ardymarky/TORCH/solidworks/rubberextrusion2.SLDPRT

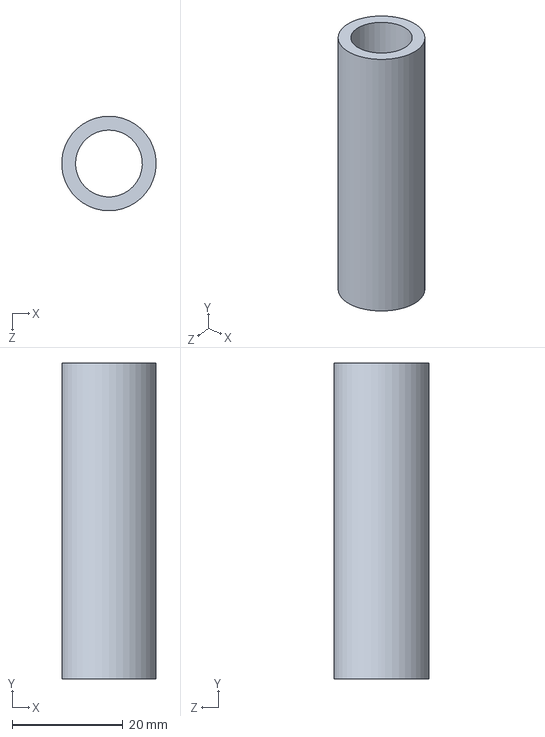
[picture p7: CAD file, 2025-04-05]
solidworks/rubberextrusion2.SLDPRT
17.0 x 57.0 x 17.0 mm
