ardymarky/TORCH/solidworks/tpu_extrusion2.SLDPRT

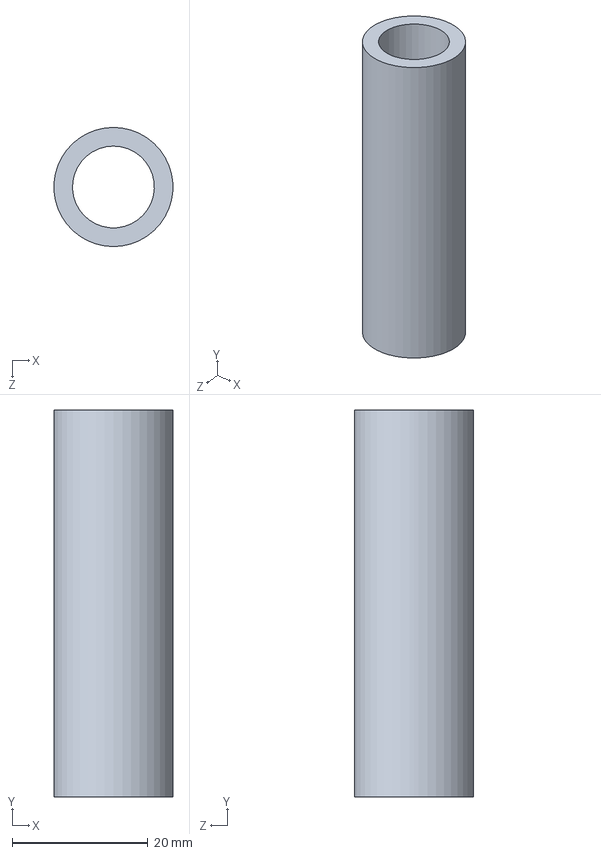
[picture p8: CAD file, 2025-04-05]
solidworks/tpu_extrusion2.SLDPRT
17.5 x 57.0 x 17.6 mm
