ardymarky/TORCH/solidworks/tpu_extrusion.SLDPRT

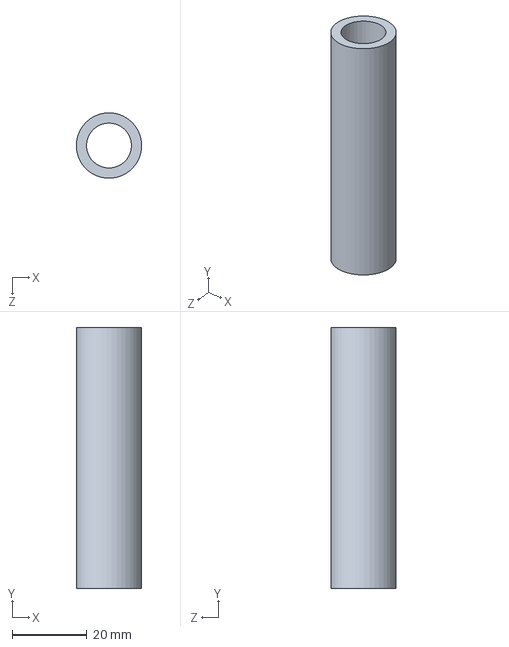
[picture p9: CAD file, 2025-04-05]
solidworks/tpu_extrusion.SLDPRT
17.5 x 70.0 x 17.5 mm
