ardymarky/TORCH/solidworks/endstop_2point0_1.SLDPRT

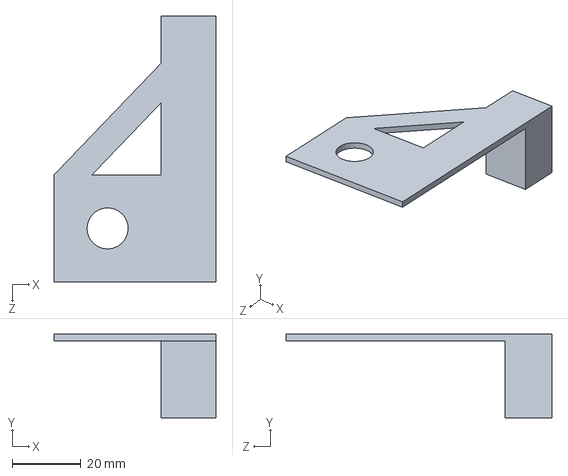
[picture p10: CAD file, 2025-04-04]
solidworks/endstop_2point0_1.SLDPRT
47.3 x 24.5 x 77.6 mm
