ardymarky/TORCH/solidworks/endstop_lidar.SLDPRT

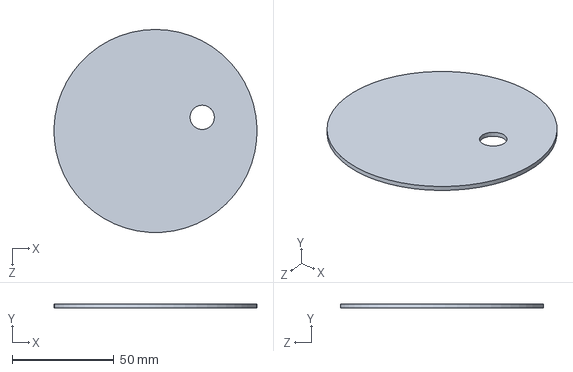
[picture p11: CAD file, 2025-04-04]
solidworks/endstop_lidar.SLDPRT
100.0 x 2.00 x 100.0 mm
