ardymarky/TORCH/solidworks/AC_DC_TOP_PLATE.SLDPRT

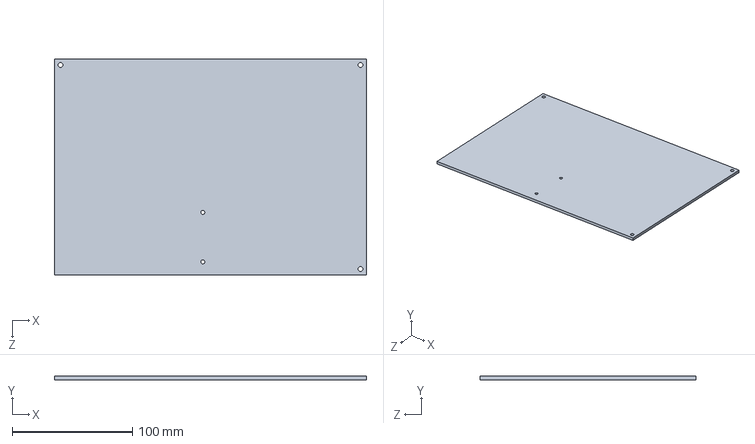
[picture p12: CAD file, 2025-04-02]
solidworks/AC_DC_TOP_PLATE.SLDPRT
260.0 x 3.00 x 180.0 mm
