ardymarky/TORCH/solidworks/xrailmount.SLDPRT

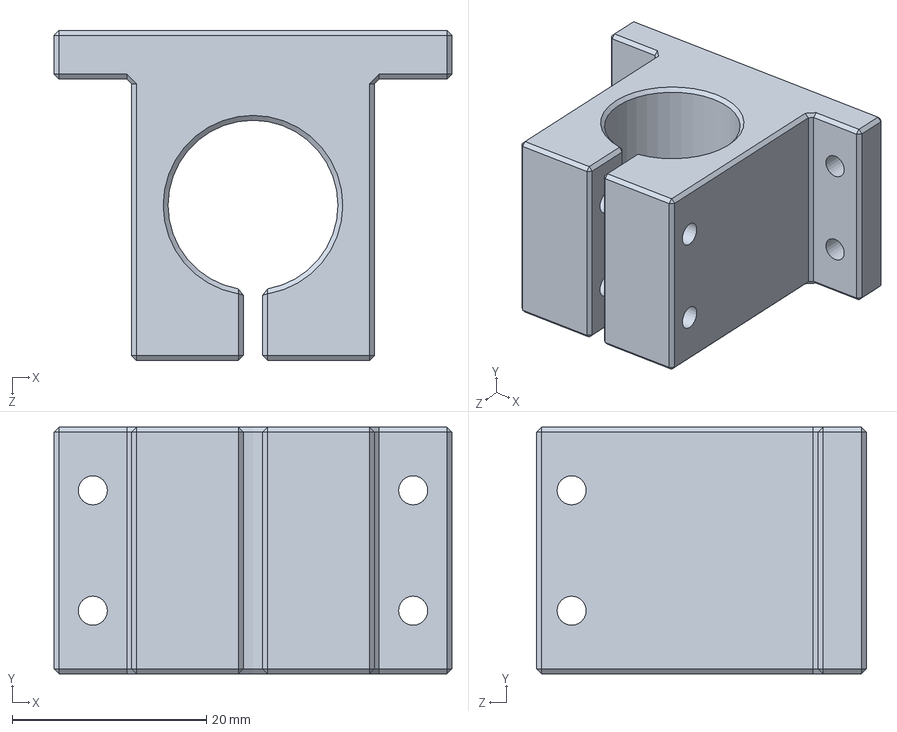
[picture p13: CAD file, 2025-03-26]
solidworks/xrailmount.SLDPRT
41.0 x 25.4 x 34.0 mm
