ardymarky/TORCH/solidworks/dronewiring.SLDPRT

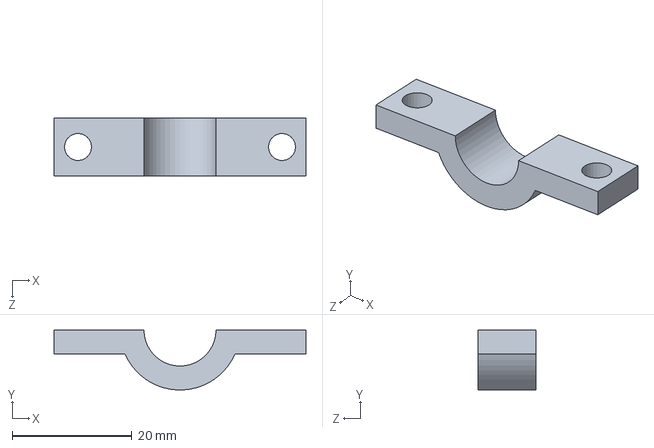
[picture p14: CAD file, 2025-03-26]
solidworks/dronewiring.SLDPRT
42.0 x 9.98 x 9.75 mm
