ardymarky/TORCH/solidworks/Linear_rail_hold_V4_2_new.SLDPRT

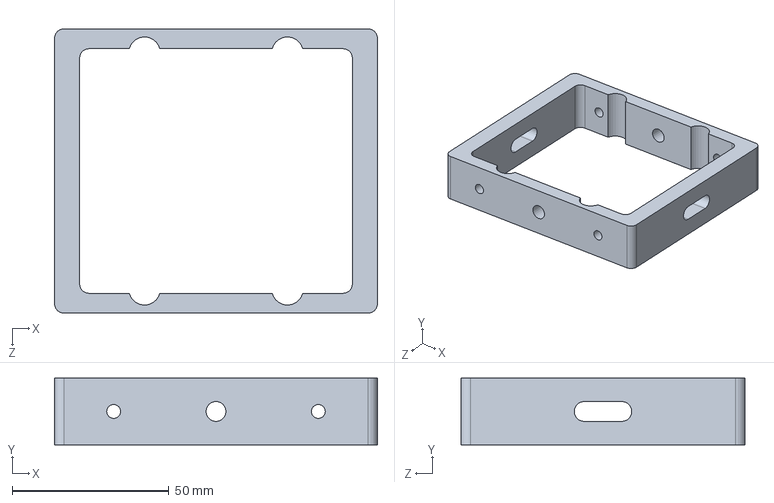
[picture p15: CAD file, 2025-03-25]
solidworks/Linear_rail_hold_V4_2_new.SLDPRT
103.0 x 21.3 x 90.7 mm
