ardymarky/TORCH/solidworks/dronewirehinge.SLDPRT

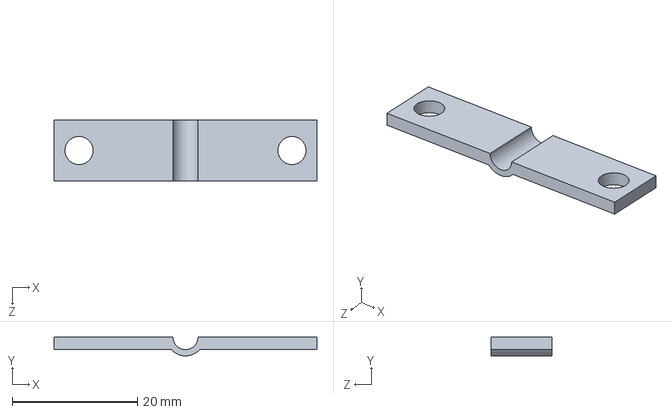
[picture p16: CAD file, 2025-03-25]
solidworks/dronewirehinge.SLDPRT
42.0 x 2.99 x 9.75 mm
