ardymarky/TORCH/solidworks/Rod_mount_two holes.SLDPRT

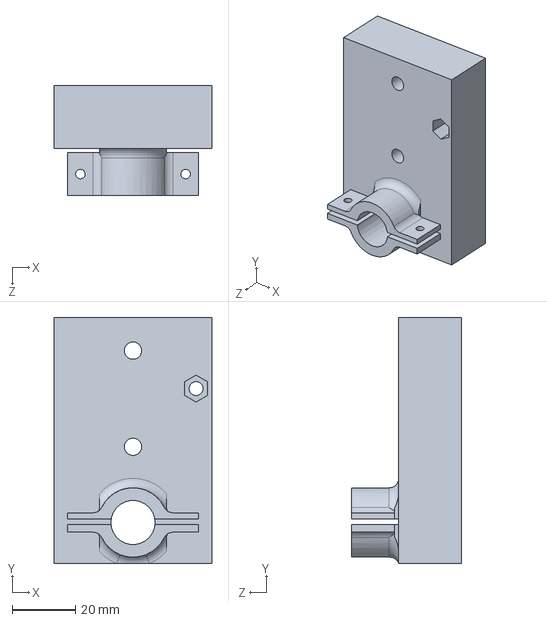
[picture p17: CAD file, 2025-03-25]
solidworks/Rod_mount_two holes.SLDPRT
50.0 x 78.0 x 35.0 mm
