ardymarky/TORCH/solidworks/Wheel_encoder_mount_two _hole.SLDPRT

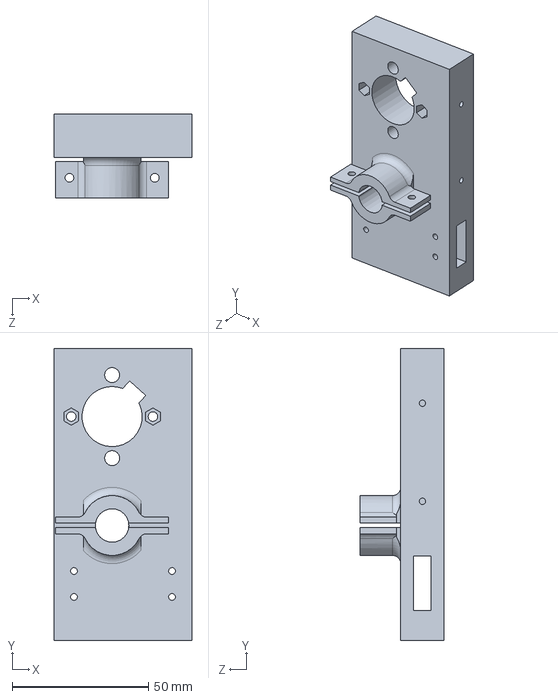
[picture p18: CAD file, 2025-03-25]
solidworks/Wheel_encoder_mount_two _hole.SLDPRT
50.6 x 107.2 x 31.0 mm
