ardymarky/TORCH/solidworks/TORCH_PULLEY_WHEEL.SLDPRT

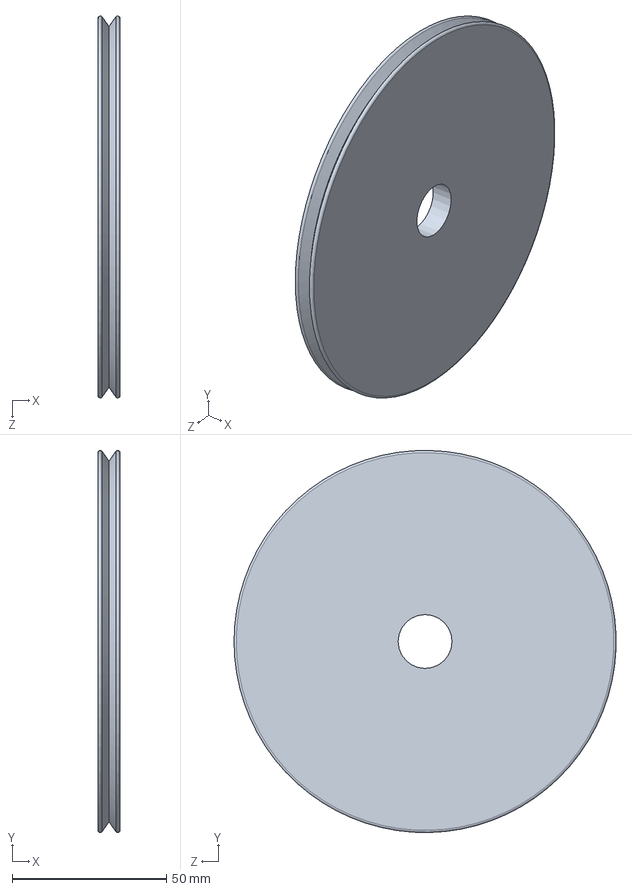
[picture p19: CAD file, 2025-03-25]
solidworks/TORCH_PULLEY_WHEEL.SLDPRT
7.14 x 123.8 x 123.8 mm
