ardymarky/TORCH/solidworks/squarerubber_1.SLDPRT

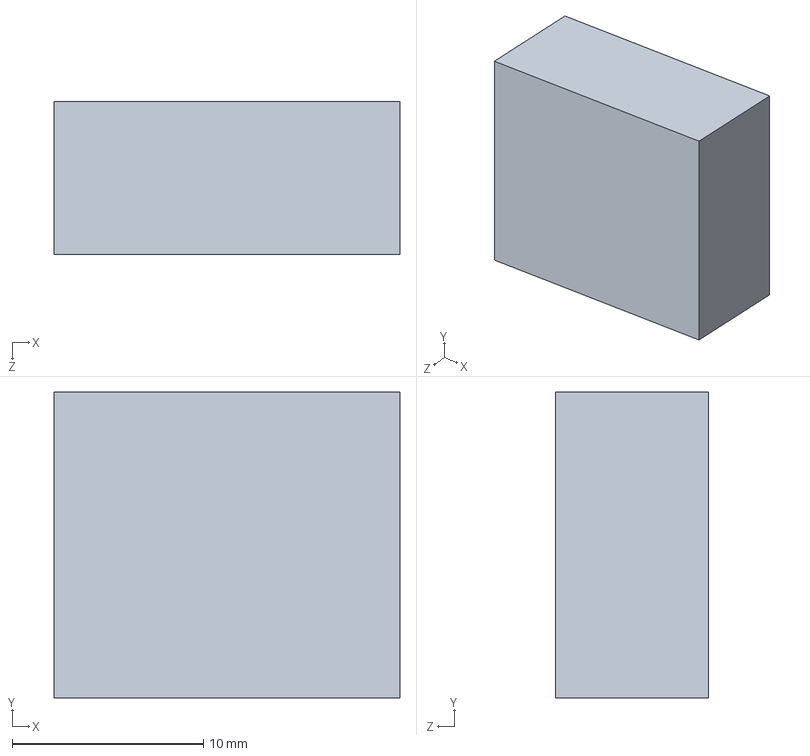
[picture p20: CAD file, 2025-03-19]
solidworks/squarerubber_1.SLDPRT
18.1 x 16.0 x 8.00 mm
