ardymarky/TORCH/solidworks/squarerubber.SLDPRT

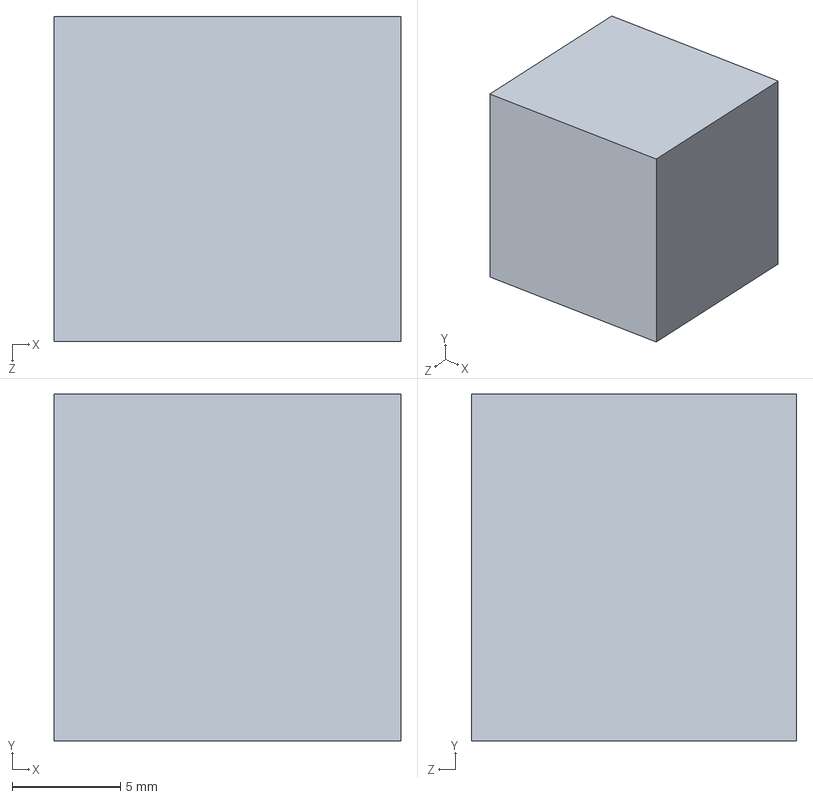
[picture p21: CAD file, 2025-03-19]
solidworks/squarerubber.SLDPRT
16.0 x 16.0 x 15.0 mm
