ardymarky/TORCH/solidworks/Wheel_encoder_mount_carbon_rod_V2.STL

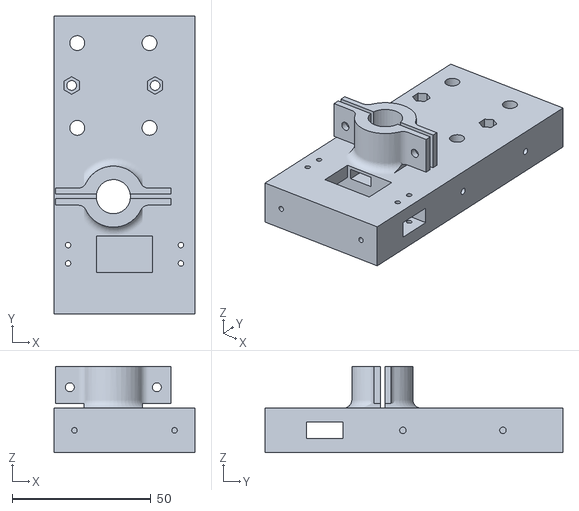
[picture p22: CAD file, 2025-03-18]
solidworks/Wheel_encoder_mount_carbon_rod_V2.STL
50.6 x 107.2 x 31.0
