ardymarky/TORCH/solidworks/Rod_mount_carbon_rod_V2.SLDPRT

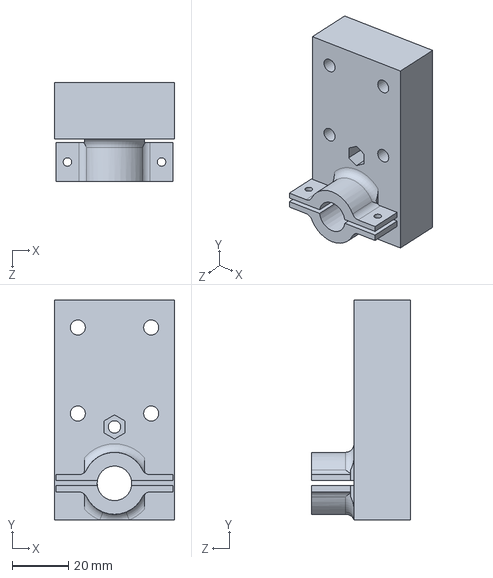
[picture p23: CAD file, 2025-03-18]
solidworks/Rod_mount_carbon_rod_V2.SLDPRT
42.6 x 78.0 x 35.0 mm
