ardymarky/TORCH/solidworks/guard_bottom1_combo.SLDPRT

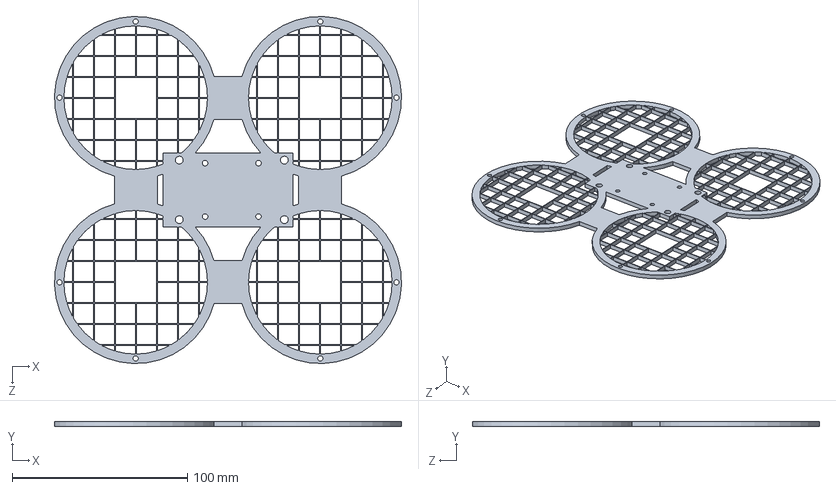
[picture p24: CAD file, 2025-03-18]
solidworks/guard_bottom1_combo.SLDPRT
198.2 x 3.00 x 198.2 mm
