ardymarky/TORCH/solidworks/tpu_piece_rod_2.SLDPRT

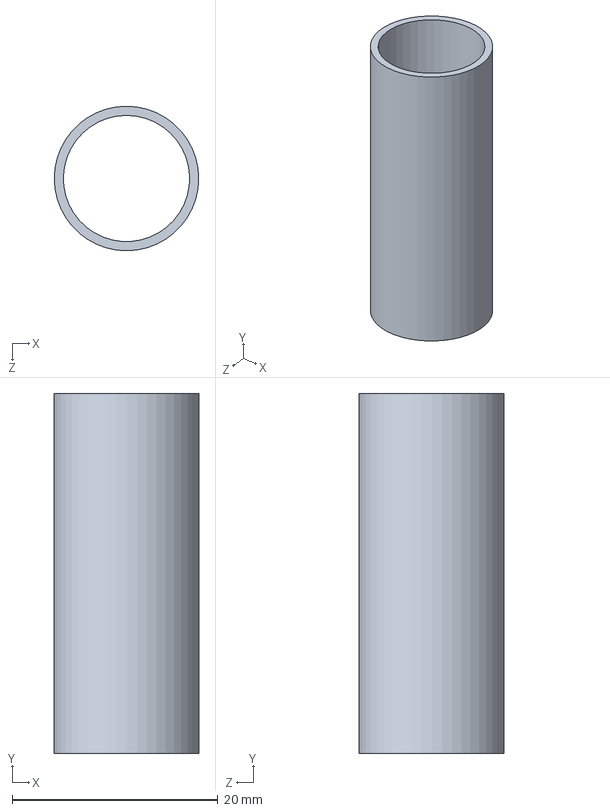
[picture p25: CAD file, 2025-03-07]
solidworks/tpu_piece_rod_2.SLDPRT
14.1 x 35.0 x 14.1 mm
