ardymarky/TORCH/solidworks/Rod_mount.SLDPRT

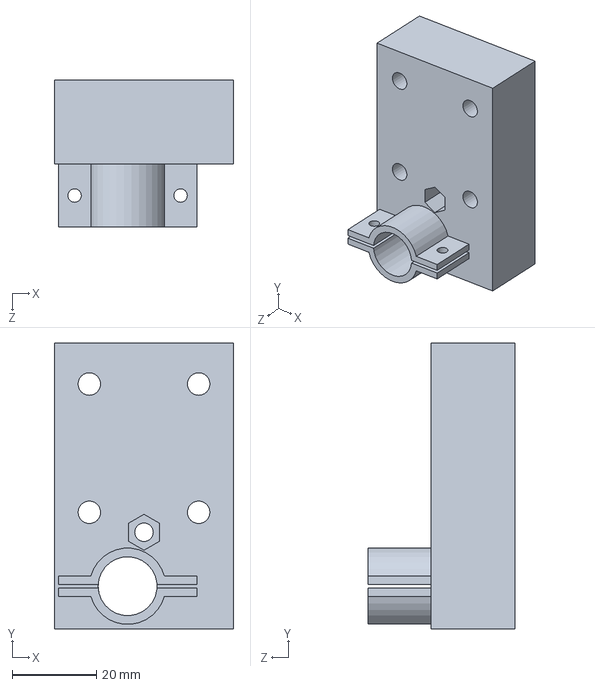
[picture p26: CAD file, 2025-03-07]
solidworks/Rod_mount.SLDPRT
42.6 x 68.0 x 35.0 mm
