ardymarky/TORCH/solidworks/Wheel_encoder_mount_v2_alteration.SLDPRT

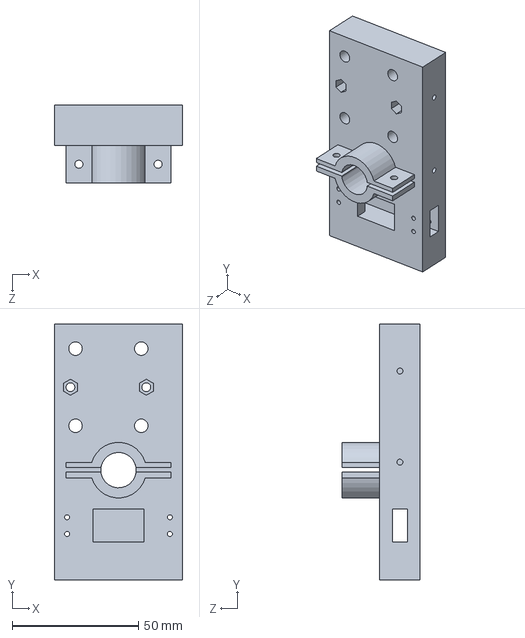
[picture p27: CAD file, 2025-03-07]
solidworks/Wheel_encoder_mount_v2_alteration.SLDPRT
50.6 x 101.2 x 31.0 mm
