ardymarky/TORCH/solidworks/tpu_piece_SMALLER.SLDPRT

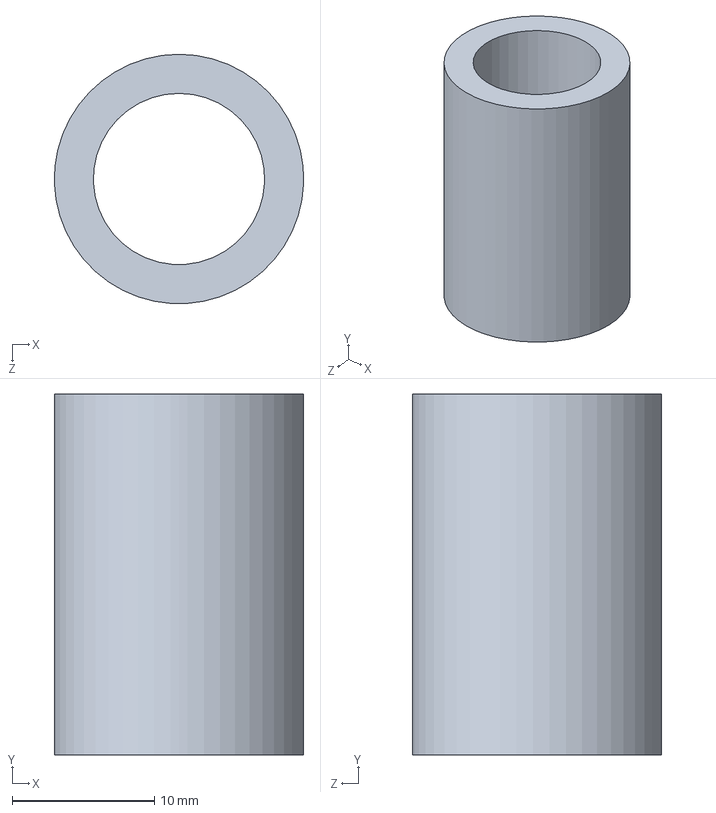
[picture p28: CAD file, 2025-03-06]
solidworks/tpu_piece_SMALLER.SLDPRT
17.5 x 25.4 x 17.6 mm
