ardymarky/TORCH/solidworks/Rod_mount_1mm_bearing_through_hole.SLDPRT

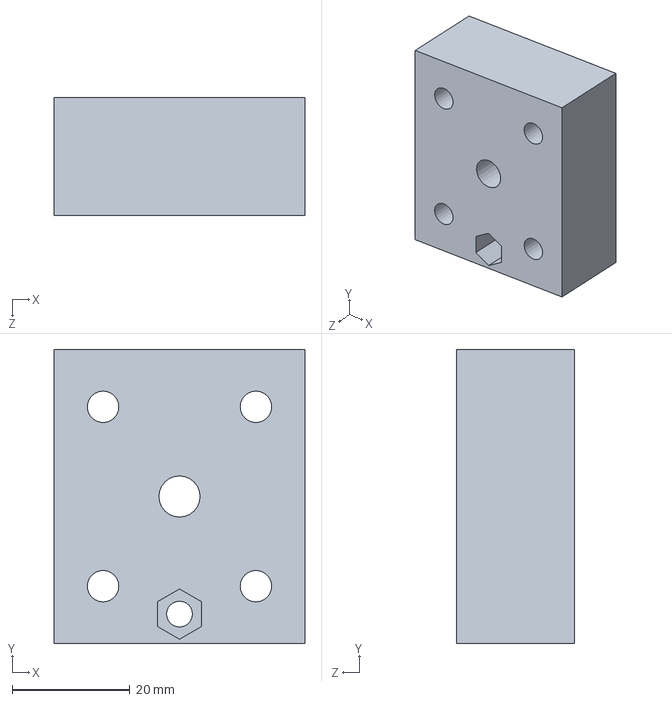
[picture p29: CAD file, 2025-03-06]
solidworks/Rod_mount_1mm_bearing_through_hole.SLDPRT
42.6 x 50.0 x 20.0 mm
