ardymarky/TORCH/solidworks/tpu_piece_rod.SLDPRT

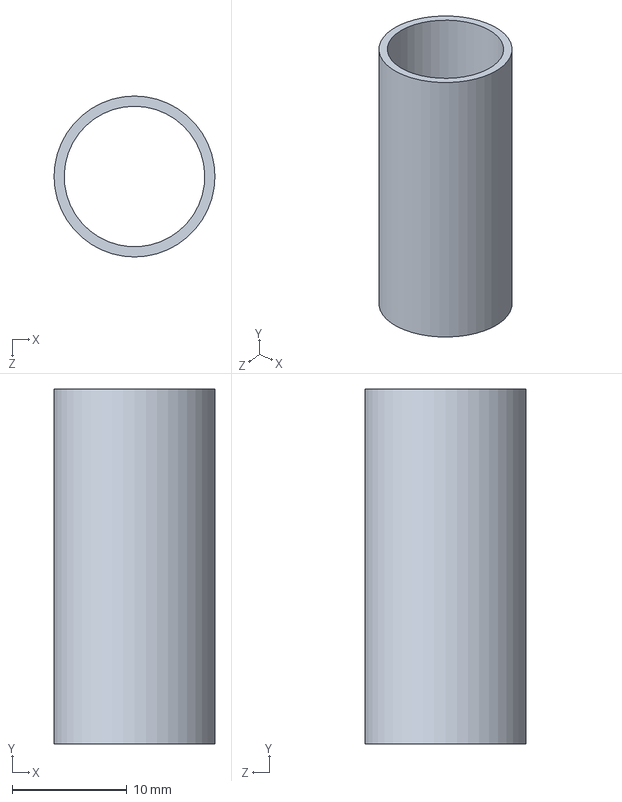
[picture p30: CAD file, 2025-03-06]
solidworks/tpu_piece_rod.SLDPRT
14.1 x 31.0 x 14.1 mm
