ardymarky/TORCH/solidworks/Wheel_encoder_mount_v2_alteration_thickness.SLDPRT

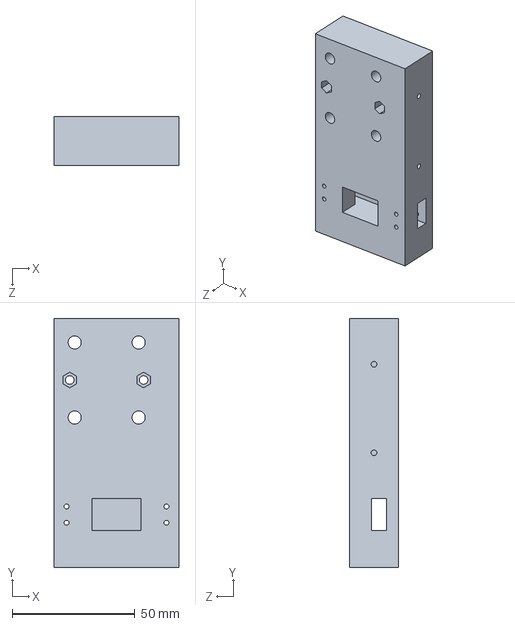
[picture p31: CAD file, 2025-02-27]
solidworks/Wheel_encoder_mount_v2_alteration_thickness.SLDPRT
50.6 x 101.2 x 20.0 mm
