ardymarky/TORCH/solidworks/clampBottomPrint.SLDPRT

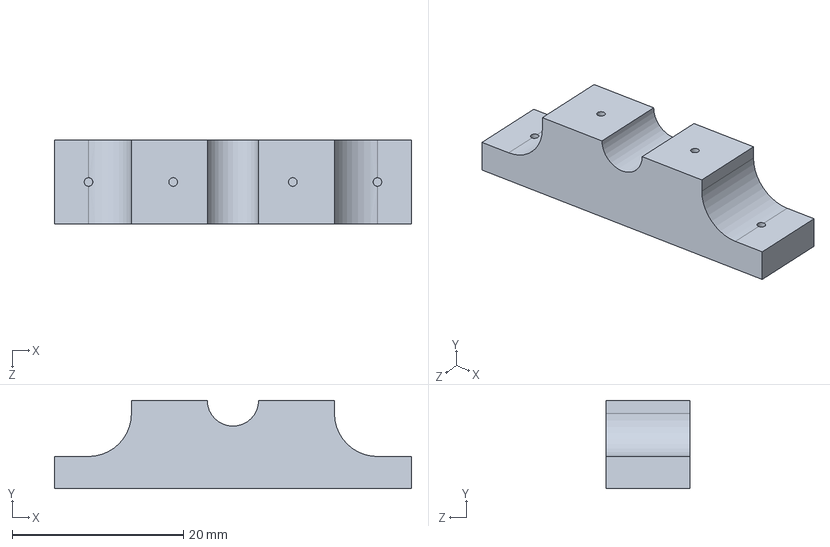
[picture p32: CAD file, 2025-02-19]
solidworks/clampBottomPrint.SLDPRT
41.7 x 10.3 x 9.87 mm
