ardymarky/TORCH/solidworks/quadBasePrintedClamps.SLDPRT

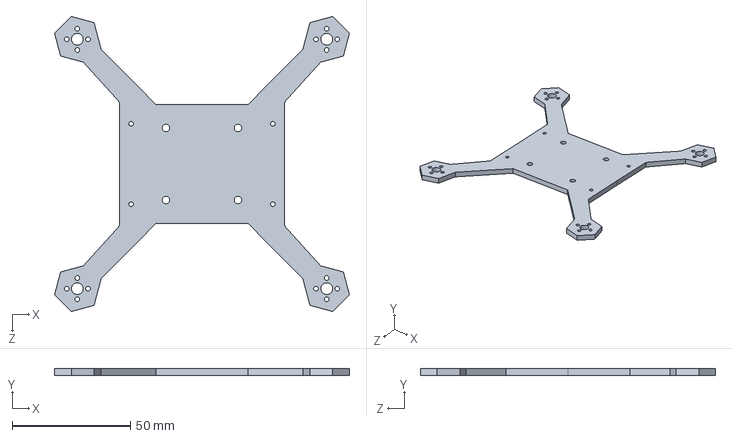
[picture p33: CAD file, 2025-02-19]
solidworks/quadBasePrintedClamps.SLDPRT
124.8 x 3.00 x 124.8 mm
