ardymarky/TORCH/solidworks/clampTopPrint.SLDPRT

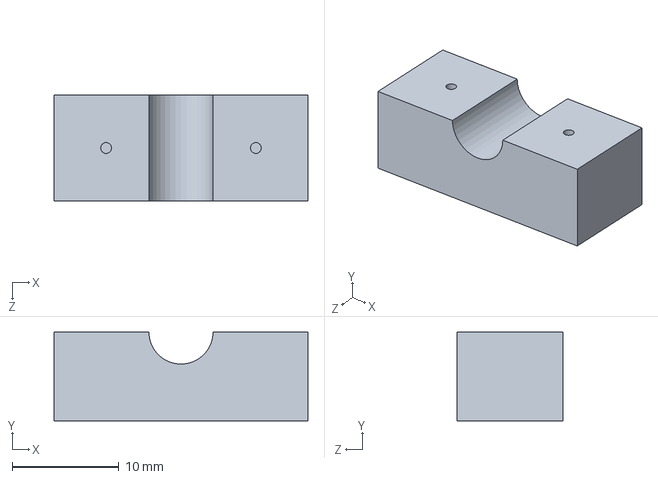
[picture p34: CAD file, 2025-02-19]
solidworks/clampTopPrint.SLDPRT
23.7 x 8.32 x 9.87 mm
