ardymarky/TORCH/solidworks/xlinearrailmount.SLDPRT

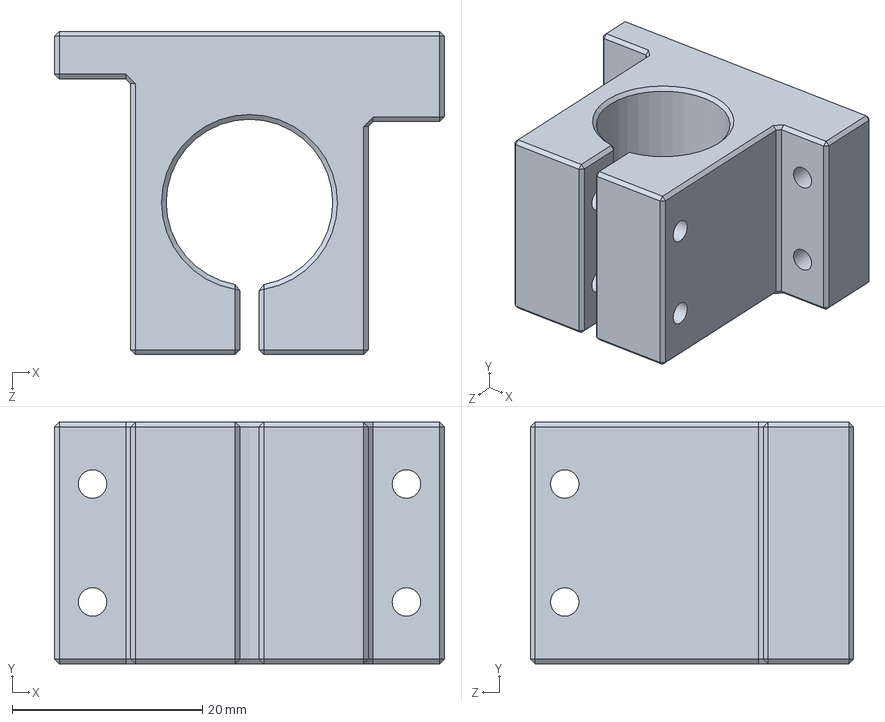
[picture p35: CAD file, 2025-02-06]
solidworks/xlinearrailmount.SLDPRT
41.0 x 25.4 x 34.0 mm
