ardymarky/TORCH/solidworks/Shaft support SK12.SLDPRT

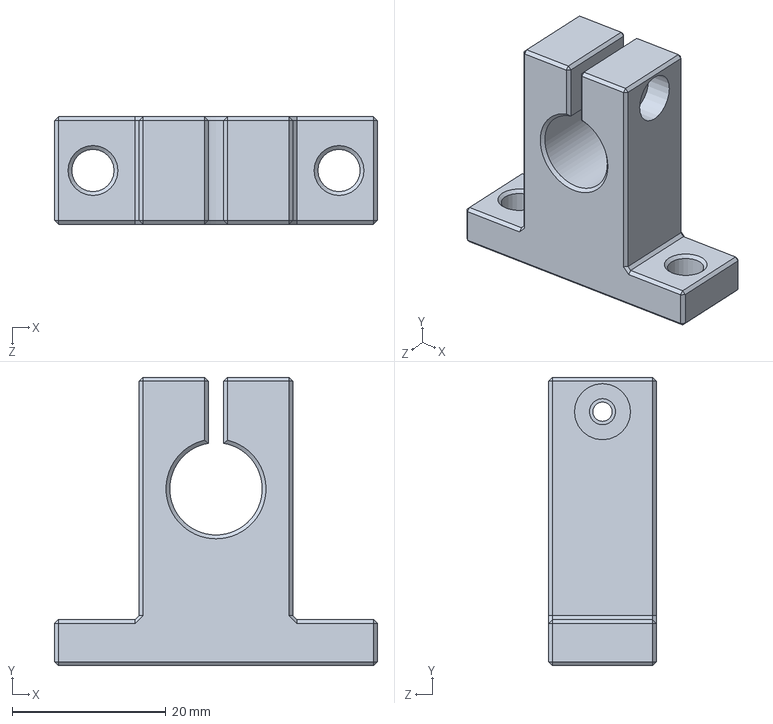
[picture p36: CAD file, 2025-02-06]
solidworks/Shaft support SK12.SLDPRT
42.0 x 37.5 x 14.0 mm
