ardymarky/TORCH/solidworks/endstop_2point0.SLDPRT

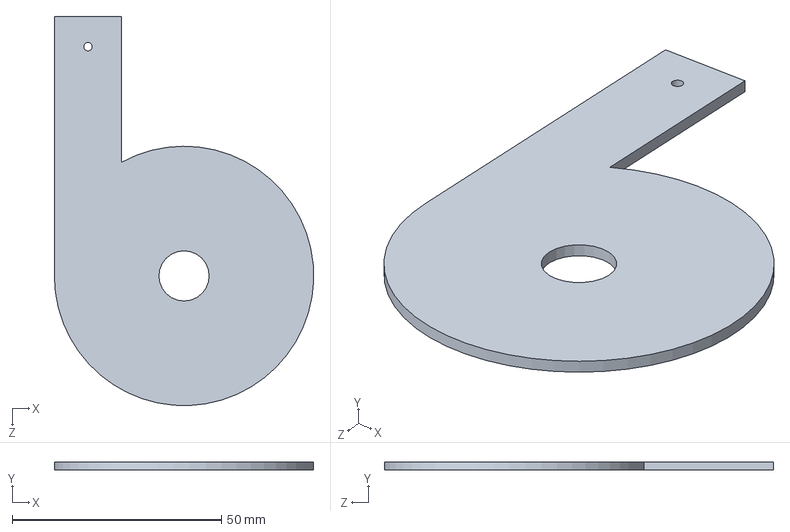
[picture p37: CAD file, 2025-01-28]
solidworks/endstop_2point0.SLDPRT
62.0 x 2.00 x 93.0 mm
