ardymarky/TORCH/solidworks/AC_DC_TOP_PLATE_STANDOFF.SLDPRT

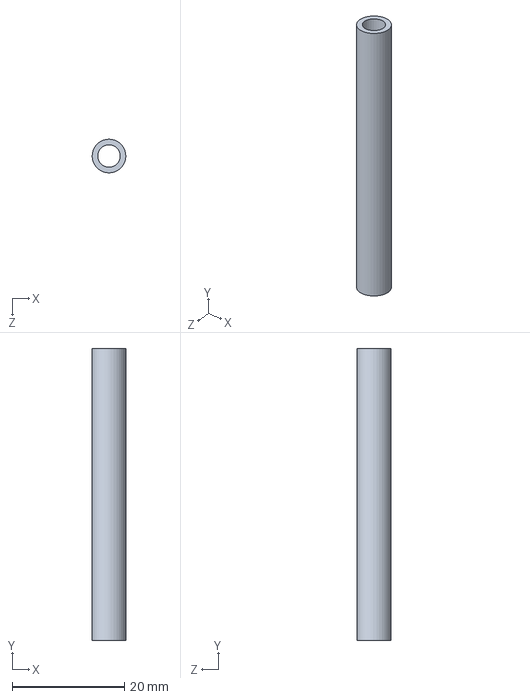
[picture p38: CAD file, 2024-12-06]
solidworks/AC_DC_TOP_PLATE_STANDOFF.SLDPRT
5.99 x 52.0 x 6.00 mm
