ardymarky/TORCH/solidworks/Relay_Standoff.SLDPRT

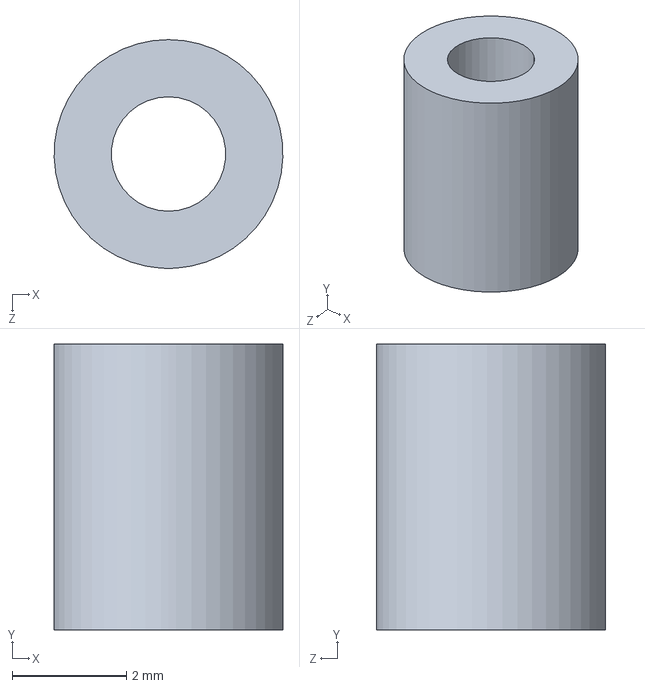
[picture p39: CAD file, 2024-12-06]
solidworks/Relay_Standoff.SLDPRT
4.00 x 5.00 x 4.00 mm
