ardymarky/TORCH/solidworks/AC_DC_Converter_Mount.SLDPRT

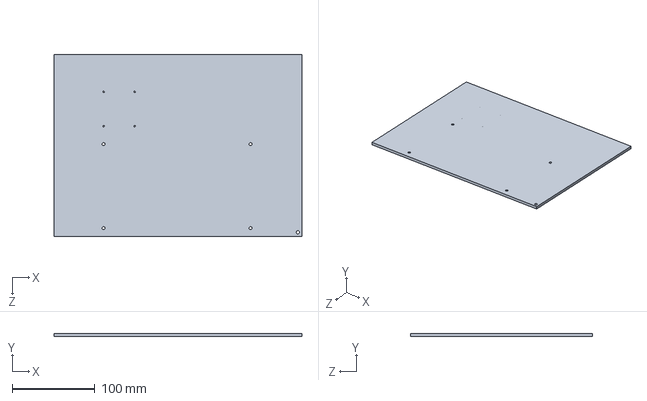
[picture p40: CAD file, 2024-12-06]
solidworks/AC_DC_Converter_Mount.SLDPRT
300.0 x 4.00 x 220.0 mm
