ardymarky/TORCH/solidworks/Relay_cover.SLDPRT

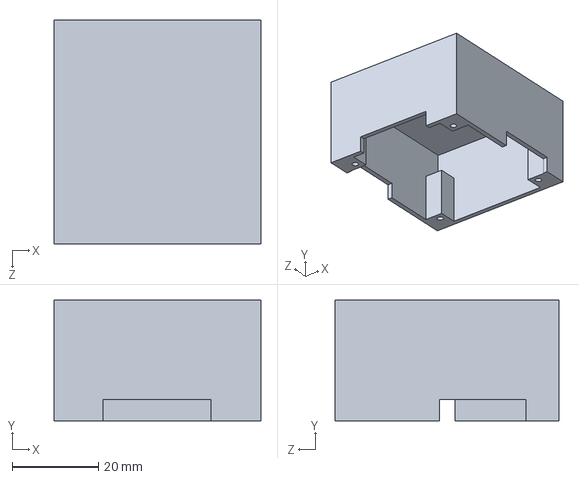
[picture p41: CAD file, 2024-12-06]
solidworks/Relay_cover.SLDPRT
48.0 x 28.0 x 52.0 mm
