ardymarky/TORCH/solidworks/PDB_Relay.SLDPRT

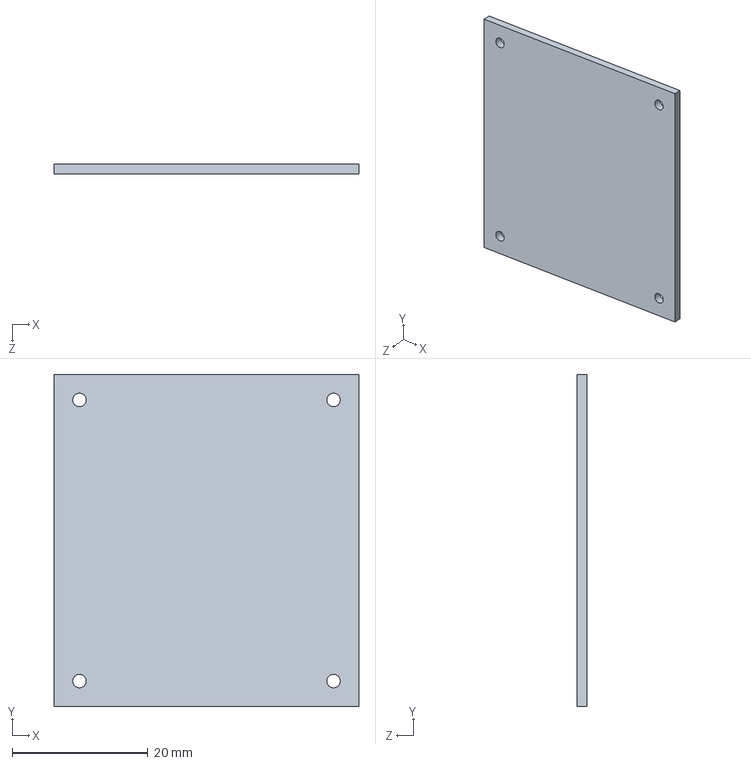
[picture p42: CAD file, 2024-12-06]
solidworks/PDB_Relay.SLDPRT
45.0 x 49.0 x 1.50 mm
