ardymarky/TORCH/solidworks/assem2.STEP

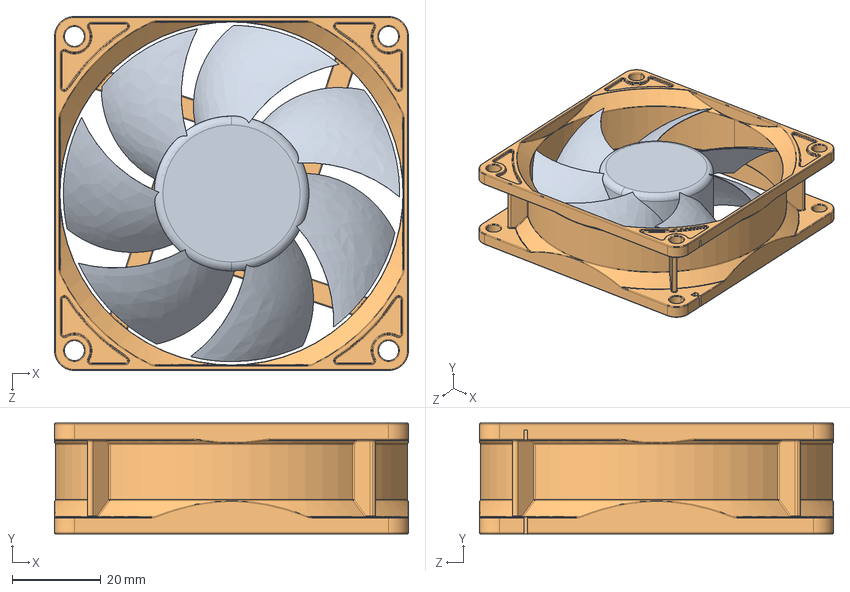
[picture p43: CAD file, 2024-12-04]
solidworks/assem2.STEP
80.0 x 25.0 x 80.0 mm
fan blades
Housing
