ardymarky/TORCH/solidworks/Power_Box.SLDPRT

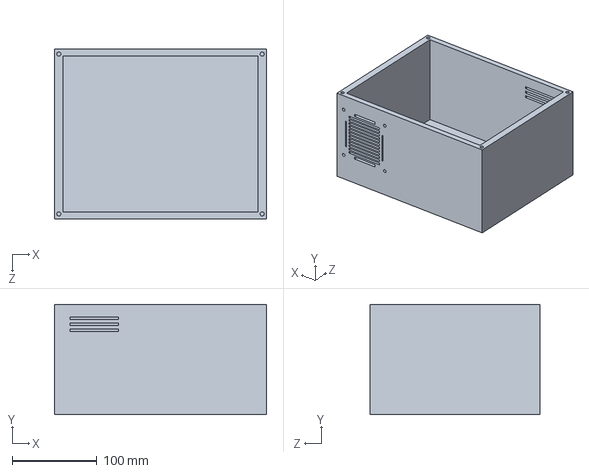
[picture p44: CAD file, 2024-12-04]
solidworks/Power_Box.SLDPRT
250.0 x 130.0 x 200.0 mm
