ardymarky/TORCH/solidworks/Pulley Wheel Standoff.STL

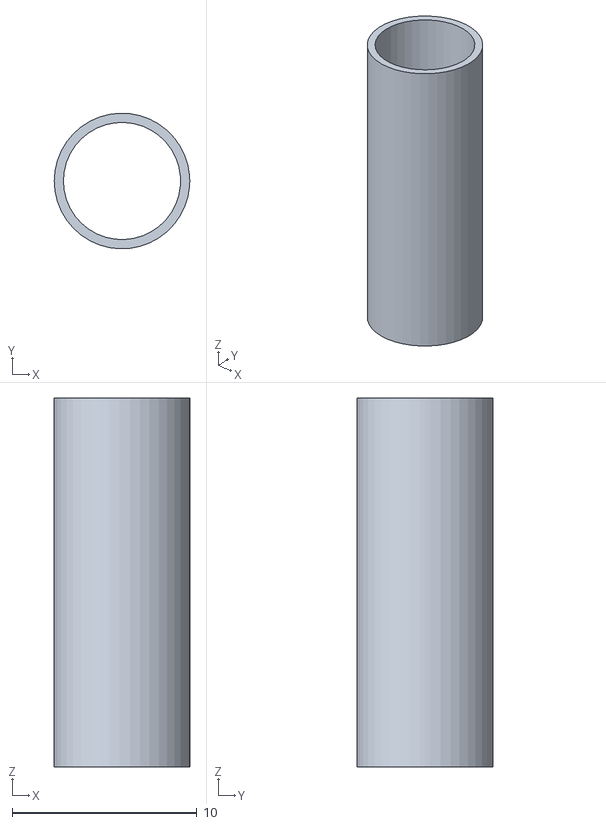
[picture p45: CAD file, 2024-12-04]
solidworks/Pulley Wheel Standoff.STL
7.35 x 7.34 x 20.0
