ardymarky/TORCH/solidworks/power connector.SLDPRT

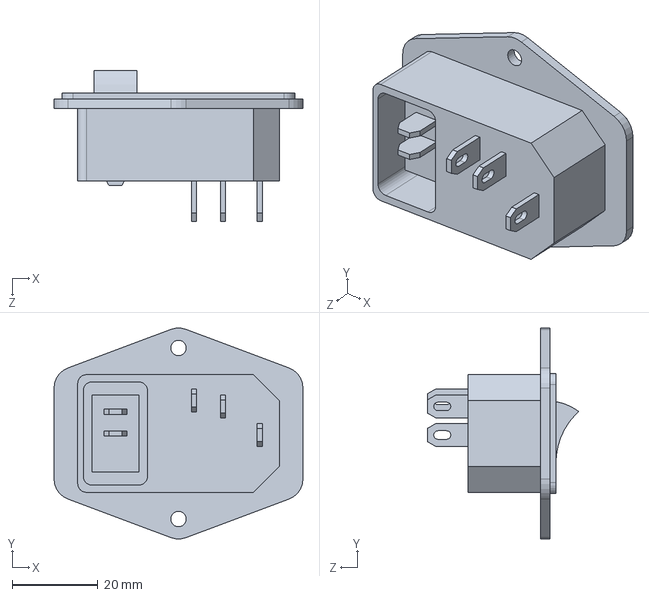
[picture p46: CAD file, 2024-12-04]
solidworks/power connector.SLDPRT
58.2 x 49.3 x 35.4 mm
