ardymarky/TORCH/solidworks/rubber_part2.SLDPRT

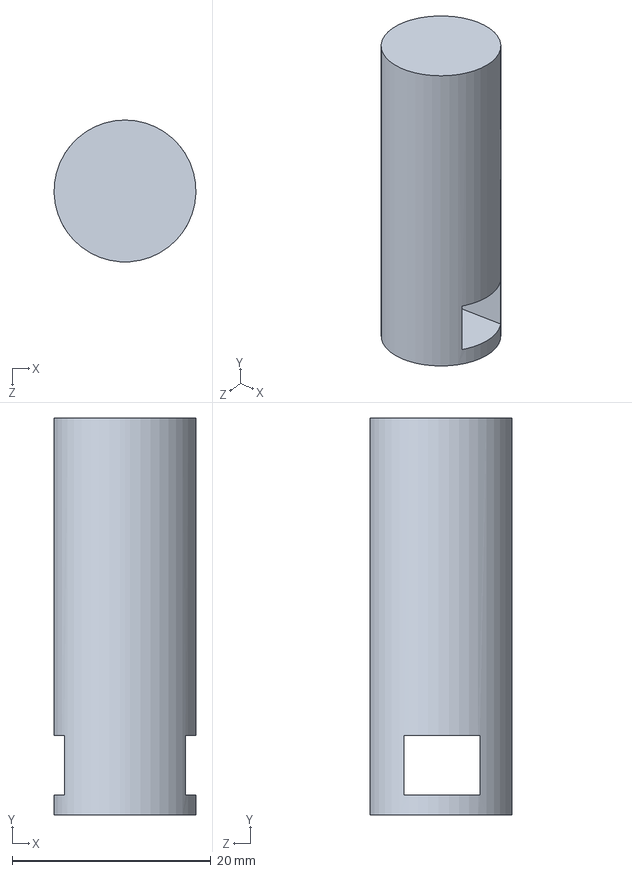
[picture p47: CAD file, 2024-12-04]
solidworks/rubber_part2.SLDPRT
14.3 x 40.0 x 14.3 mm
