ardymarky/TORCH/solidworks/rubber_p.SLDPRT

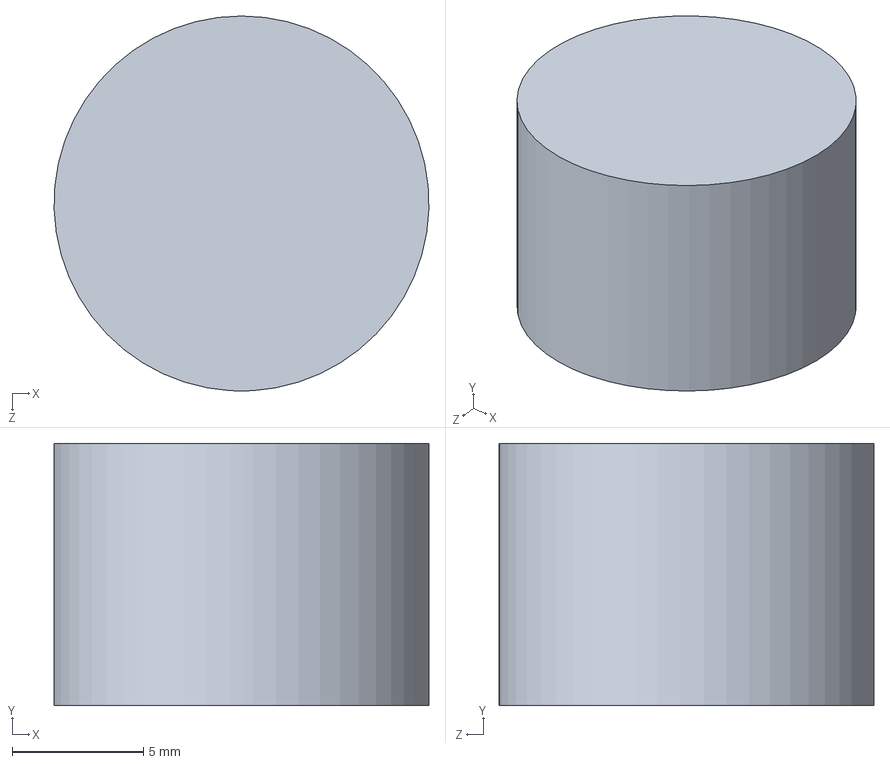
[picture p48: CAD file, 2024-11-19]
solidworks/rubber_p.SLDPRT
14.3 x 10.0 x 14.3 mm
