ardymarky/TORCH/solidworks/guard_combo.SLDPRT

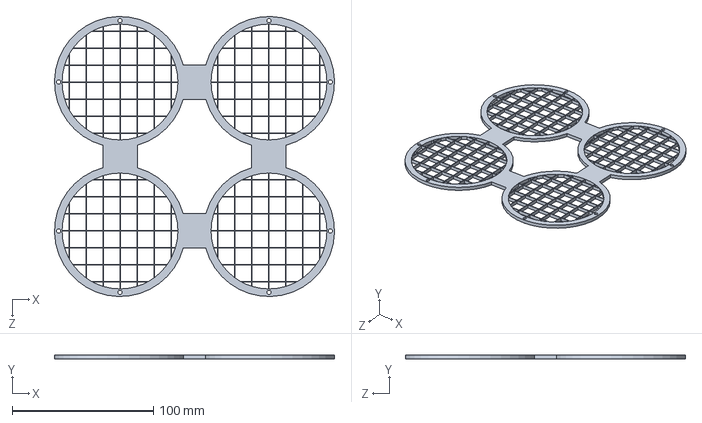
[picture p49: CAD file, 2024-11-19]
solidworks/guard_combo.SLDPRT
198.2 x 3.00 x 198.2 mm
