ardymarky/TORCH/solidworks/guard_bottom1.SLDPRT

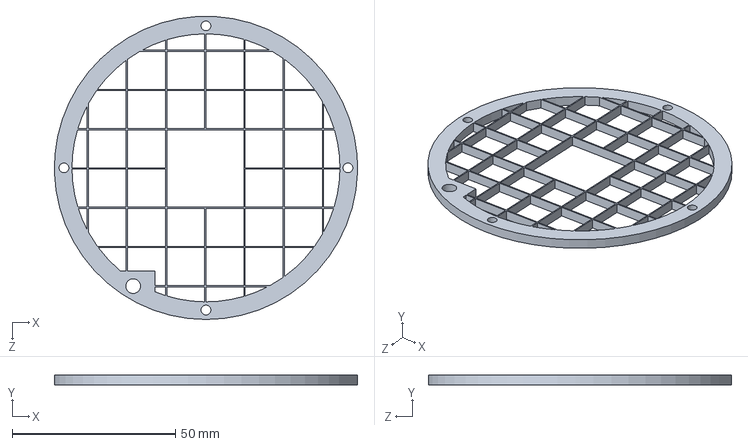
[picture p50: CAD file, 2024-11-15]
solidworks/guard_bottom1.SLDPRT
92.8 x 3.00 x 92.7 mm
