ardymarky/TORCH/solidworks/combo_3.SLDPRT

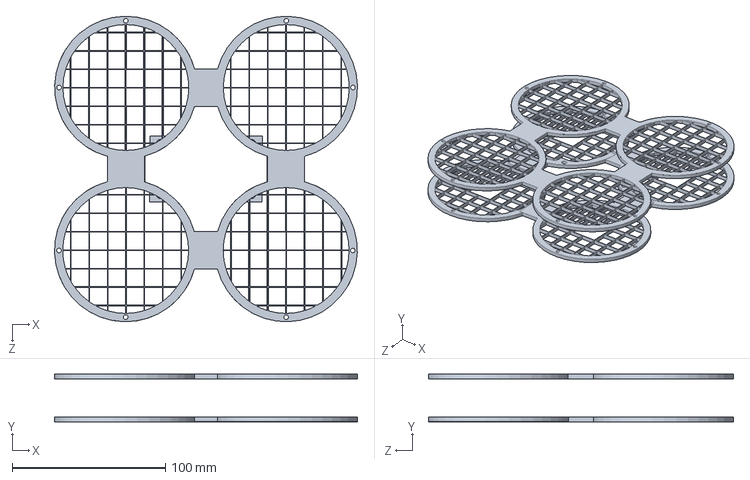
[picture p51: CAD file, 2024-11-15]
solidworks/combo_3.SLDPRT
197.4 x 31.0 x 199.0 mm
