ardymarky/TORCH/solidworks/half prop_COMBOpart.SLDPRT

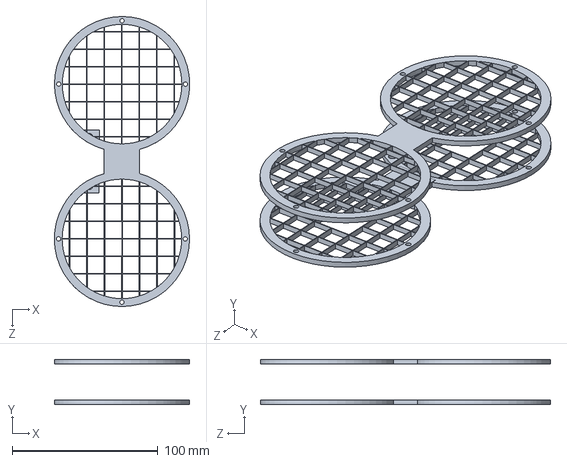
[picture p52: CAD file, 2024-11-15]
solidworks/half prop_COMBOpart.SLDPRT
92.9 x 31.0 x 199.0 mm
