ardymarky/TORCH/solidworks/combo_2.SLDPRT

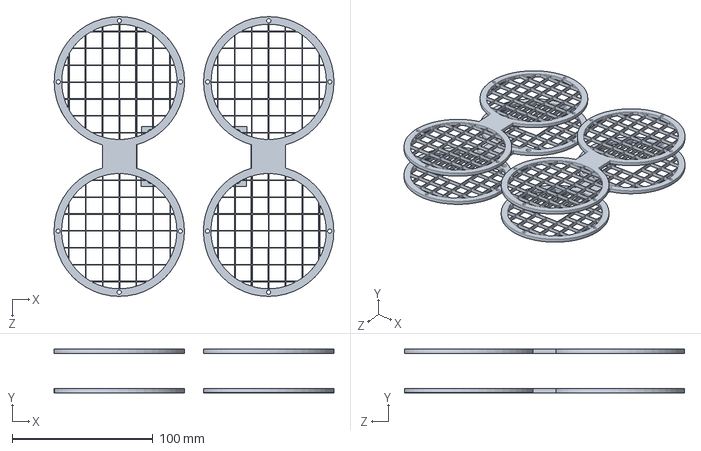
[picture p53: CAD file, 2024-11-15]
solidworks/combo_2.SLDPRT
199.2 x 31.0 x 199.0 mm
