ardymarky/TORCH/solidworks/combo.SLDPRT

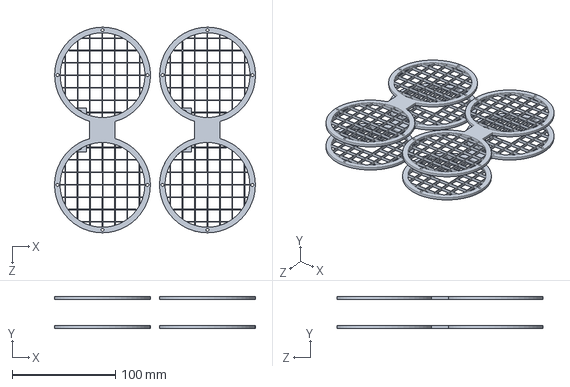
[picture p54: CAD file, 2024-11-15]
solidworks/combo.SLDPRT
194.5 x 31.0 x 199.0 mm
