ardymarky/TORCH/solidworks/guard.SLDPRT

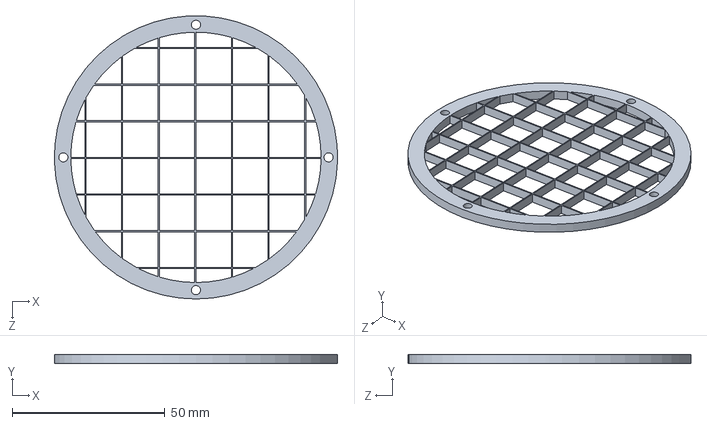
[picture p55: CAD file, 2024-11-15]
solidworks/guard.SLDPRT
92.8 x 3.00 x 92.7 mm
