ardymarky/TORCH/solidworks/stopper_lidar.SLDPRT

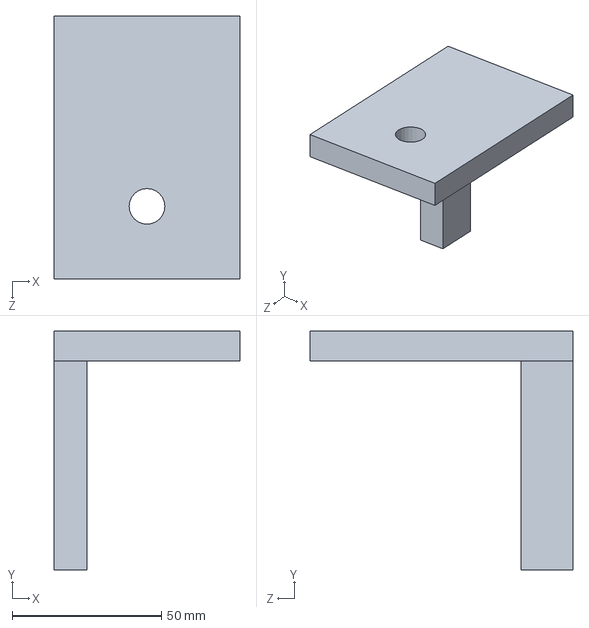
[picture p56: CAD file, 2024-11-15]
solidworks/stopper_lidar.SLDPRT
62.2 x 79.9 x 88.0 mm
