ardymarky/TORCH/solidworks/connector.SLDPRT

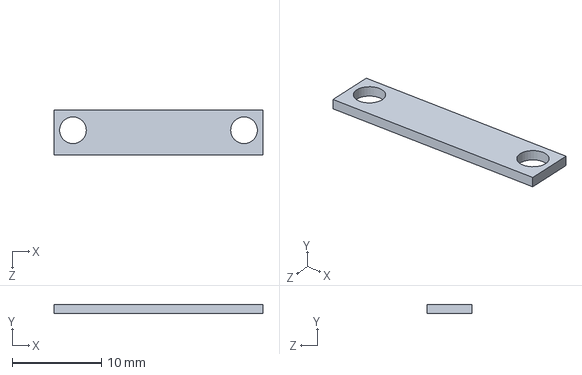
[picture p57: CAD file, 2024-11-15]
solidworks/connector.SLDPRT
23.5 x 1.00 x 5.00 mm
