ardymarky/TORCH/solidworks/guard_bottom.SLDPRT

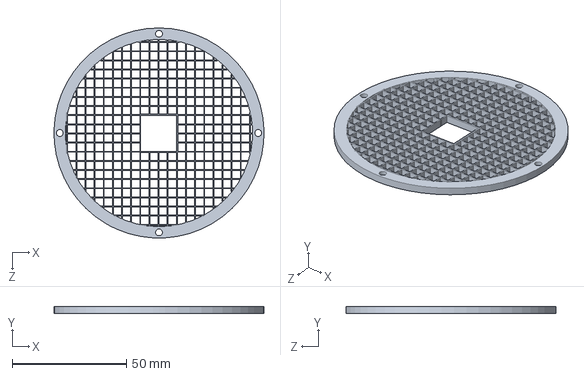
[picture p58: CAD file, 2024-11-15]
solidworks/guard_bottom.SLDPRT
92.0 x 3.00 x 92.0 mm
