ardymarky/TORCH/solidworks/connector_2.SLDPRT

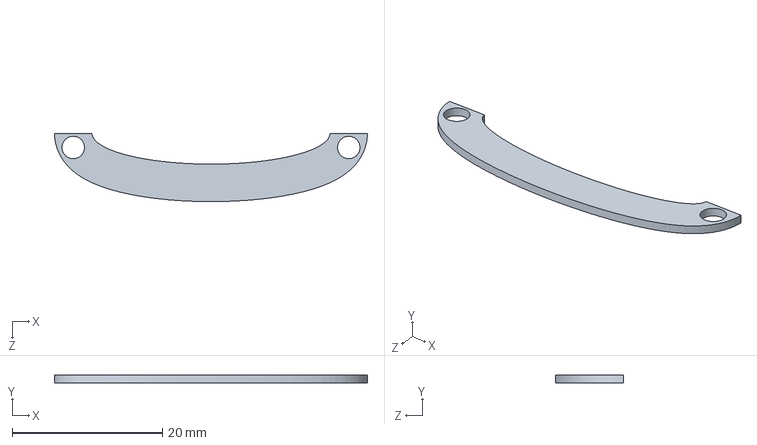
[picture p59: CAD file, 2024-11-15]
solidworks/connector_2.SLDPRT
41.7 x 1.00 x 9.09 mm
