ardymarky/TORCH/solidworks/stopper_2.SLDPRT

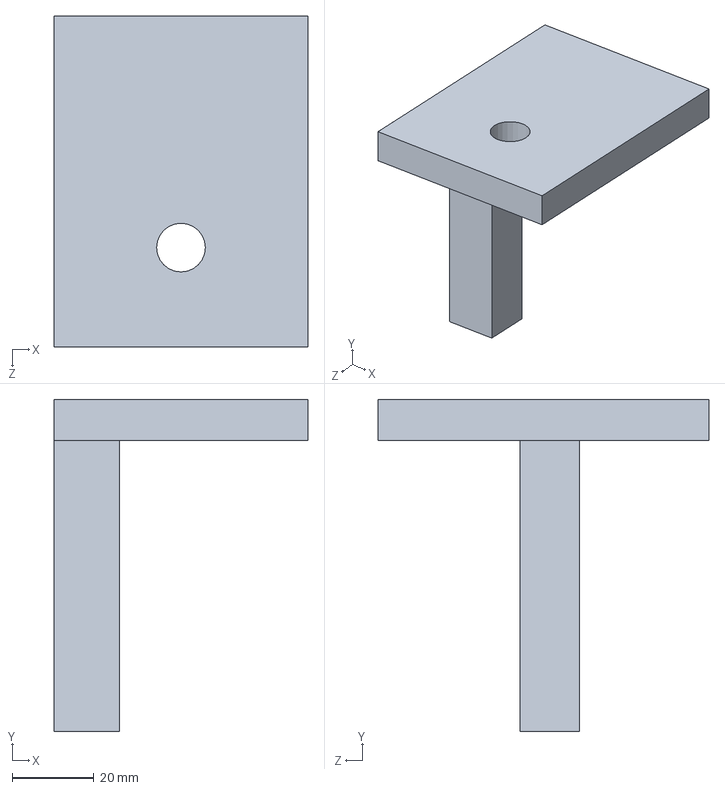
[picture p60: CAD file, 2024-11-14]
solidworks/stopper_2.SLDPRT
62.2 x 81.3 x 81.0 mm
