ardymarky/TORCH/solidworks/stopper.SLDPRT

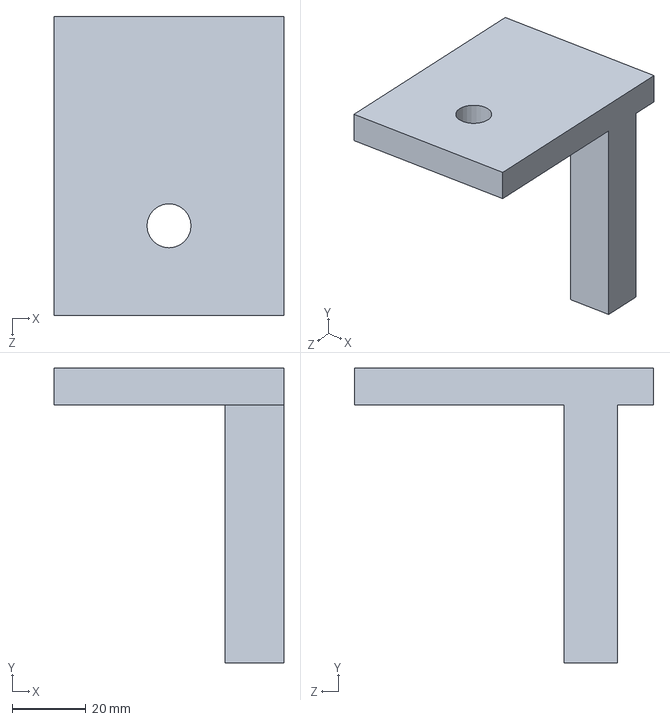
[picture p61: CAD file, 2024-11-14]
solidworks/stopper.SLDPRT
62.2 x 79.9 x 81.0 mm
