ardymarky/TORCH/solidworks/rubber.SLDPRT

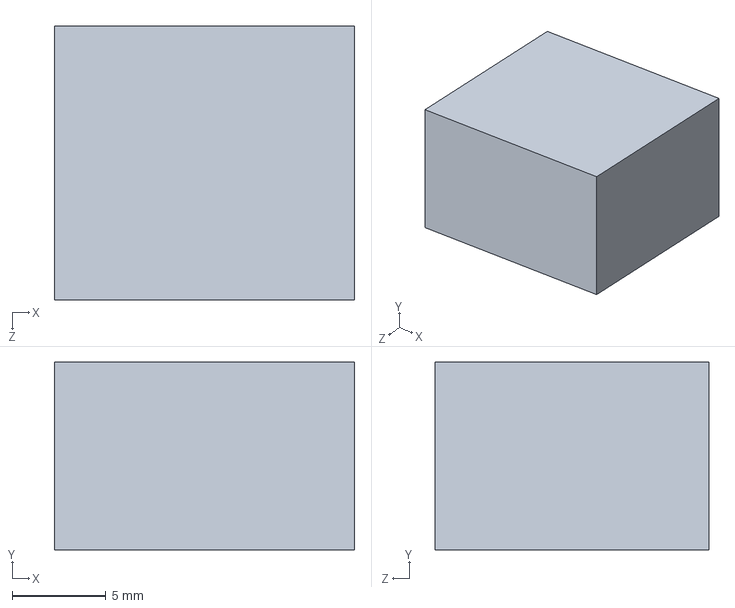
[picture p62: CAD file, 2024-11-14]
solidworks/rubber.SLDPRT
16.0 x 10.0 x 14.6 mm
