ardymarky/TORCH/solidworks/Wheel_encoder_mount_v2.SLDPRT

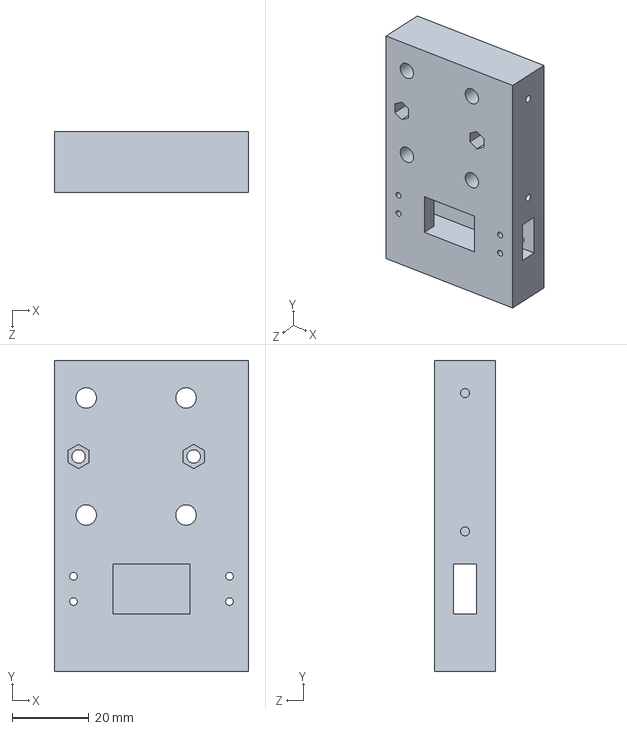
[picture p63: CAD file, 2024-11-14]
solidworks/Wheel_encoder_mount_v2.SLDPRT
50.6 x 81.0 x 16.0 mm
