ardymarky/TORCH/solidworks/rubber_lidar.SLDPRT

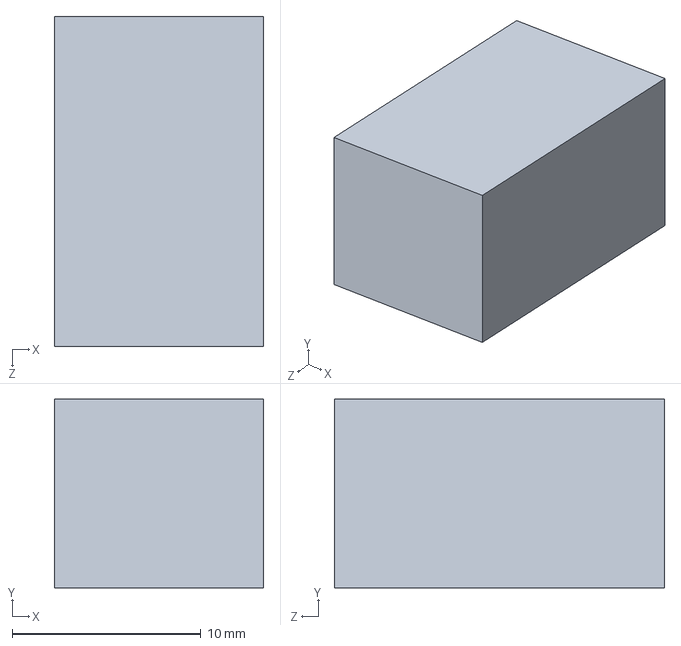
[picture p64: CAD file, 2024-11-14]
solidworks/rubber_lidar.SLDPRT
11.1 x 10.0 x 17.5 mm
