ardymarky/TORCH/solidworks/fan gaurd.SLDPRT

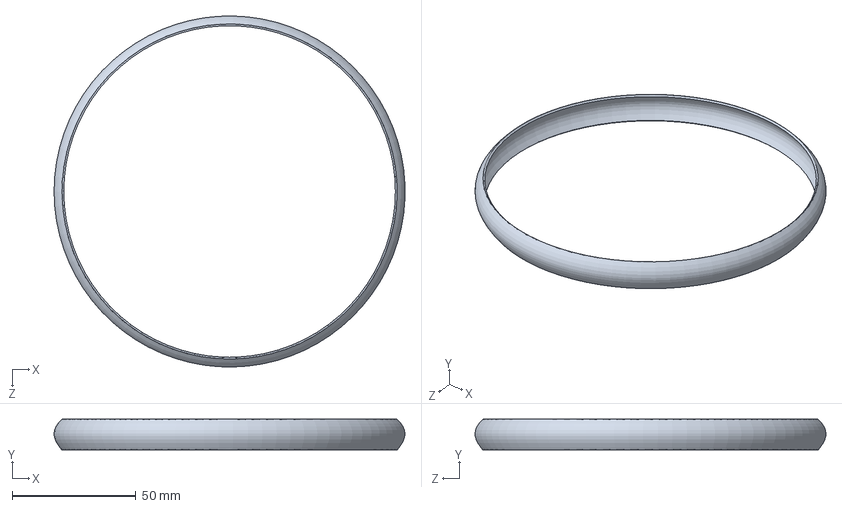
[picture p65: CAD file, 2024-11-13]
solidworks/fan gaurd.SLDPRT
141.9 x 12.5 x 142.0 mm
