ardymarky/TORCH/solidworks/V3_Tri-Loop_3-3.5-inch.SLDPRT

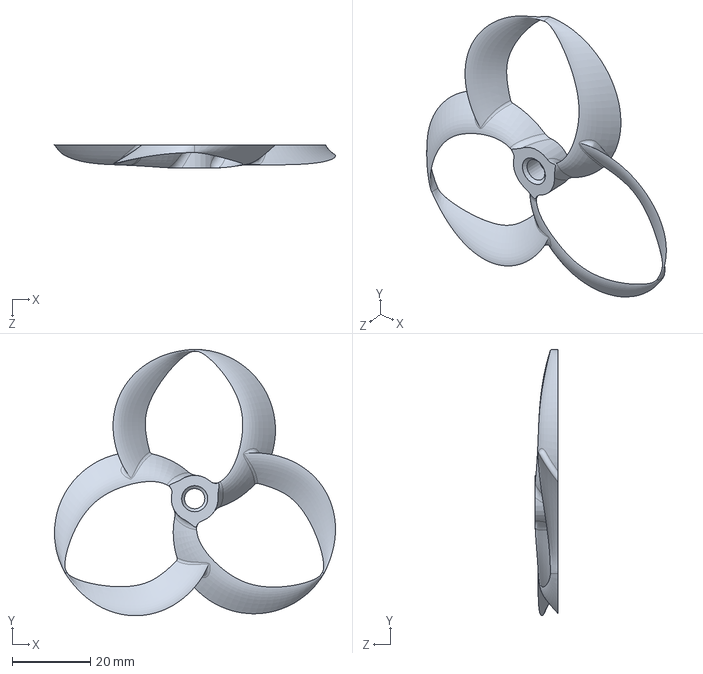
[picture p66: CAD file, 2024-11-13]
solidworks/V3_Tri-Loop_3-3.5-inch.SLDPRT
72.0 x 68.2 x 6.00 mm
