ardymarky/TORCH/solidworks/innerrail - Linear_rail_hold_V4-2.STL

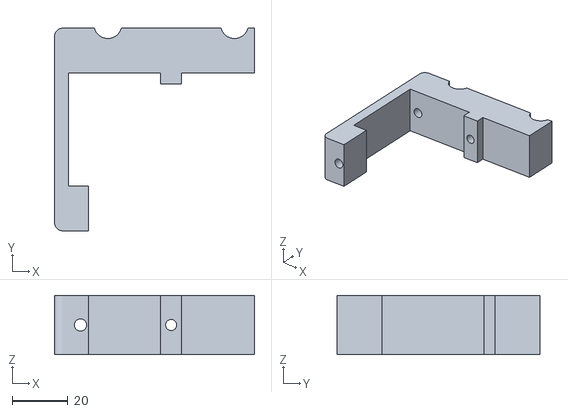
[picture p67: CAD file, 2024-11-08]
solidworks/innerrail - Linear_rail_hold_V4-2.STL
72.0 x 73.0 x 21.3
