ardymarky/TORCH/solidworks/J115F11C12VDCSH.9--3DModel-STEP-56544.STEP

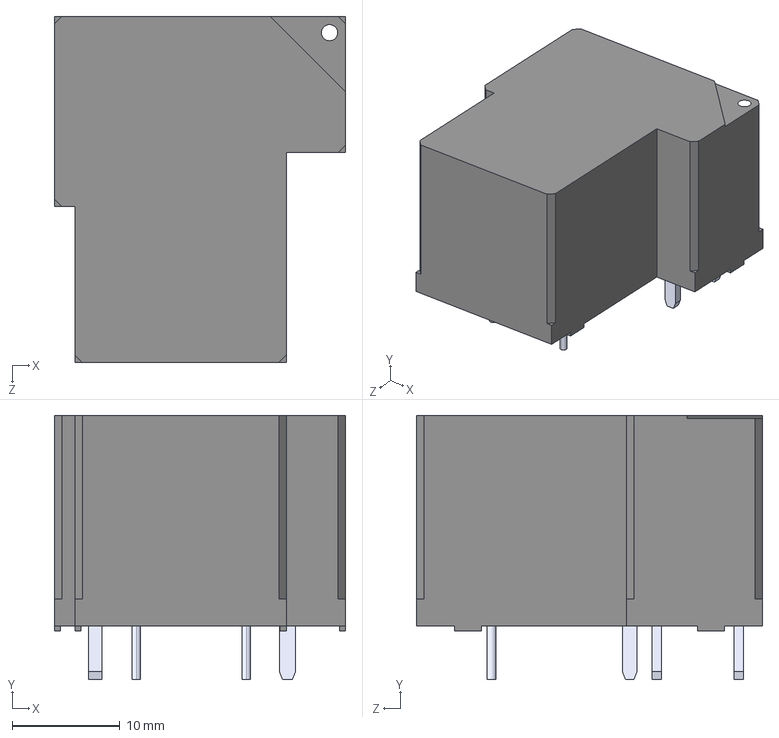
[picture p68: CAD file, 2024-10-24]
solidworks/J115F11C12VDCSH.9--3DModel-STEP-56544.STEP
27.0 x 24.5 x 32.1 mm
