ardymarky/TORCH/solidworks/Linear_rail_hold_V4_4.SLDPRT

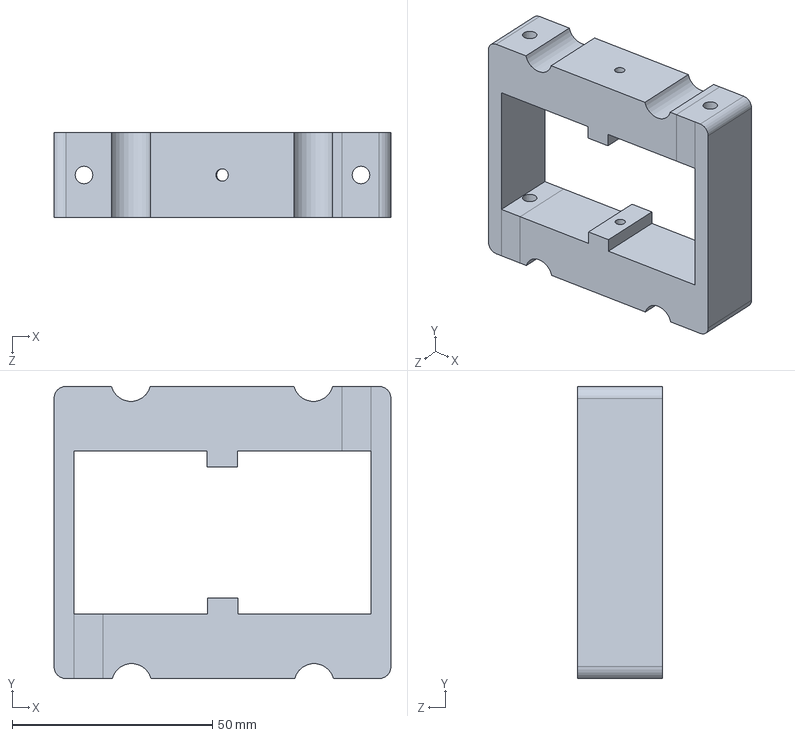
[picture p69: CAD file, 2024-10-23]
solidworks/Linear_rail_hold_V4_4.SLDPRT
84.2 x 73.0 x 21.3 mm
