ardymarky/TORCH/solidworks/40 end cap.SLDPRT

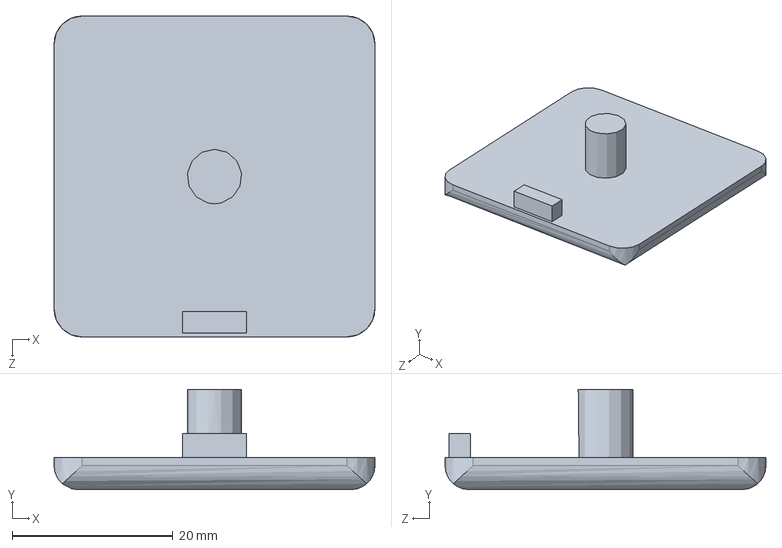
[picture p70: CAD file, 2024-10-22]
solidworks/40 end cap.SLDPRT
40.0 x 12.5 x 40.0 mm
