ardymarky/TORCH/solidworks/Button Housing [ZB4BZ102].SLDPRT

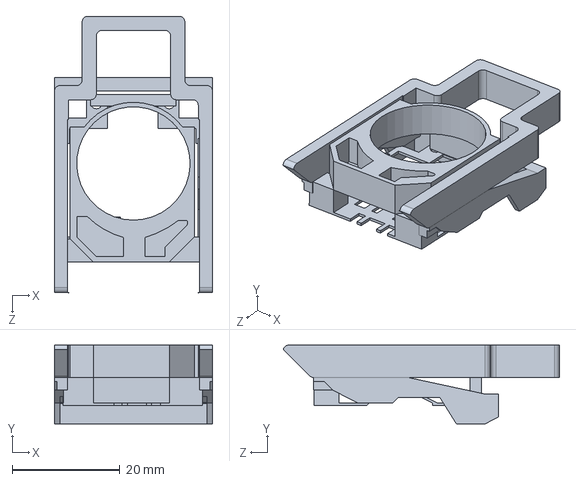
[picture p71: CAD file, 2024-10-19]
solidworks/Button Housing [ZB4BZ102].SLDPRT
29.3 x 14.6 x 51.2 mm
