ardymarky/TORCH/solidworks/NC Contact [ZBE-102].SLDPRT

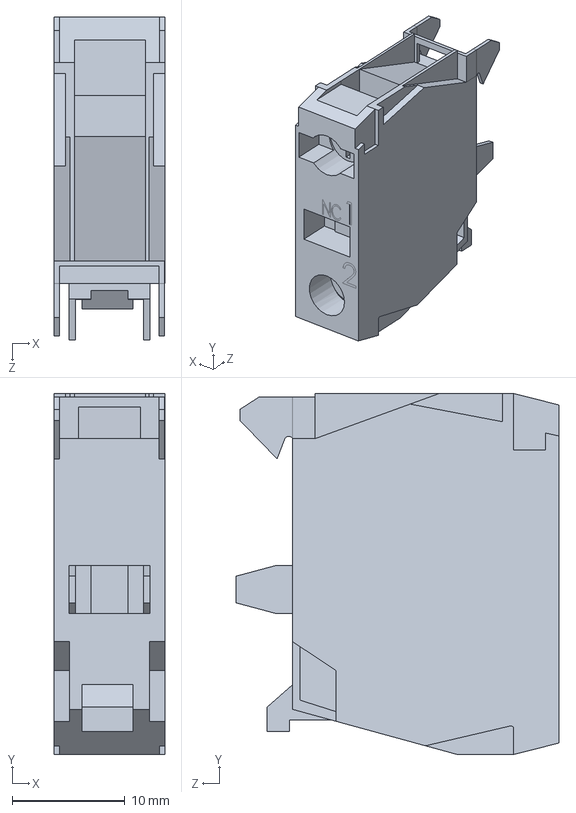
[picture p72: CAD file, 2024-10-19]
solidworks/NC Contact [ZBE-102].SLDPRT
9.83 x 32.0 x 28.6 mm
