ardymarky/TORCH/solidworks/E-Stop Button [ZB4BS844].SLDPRT

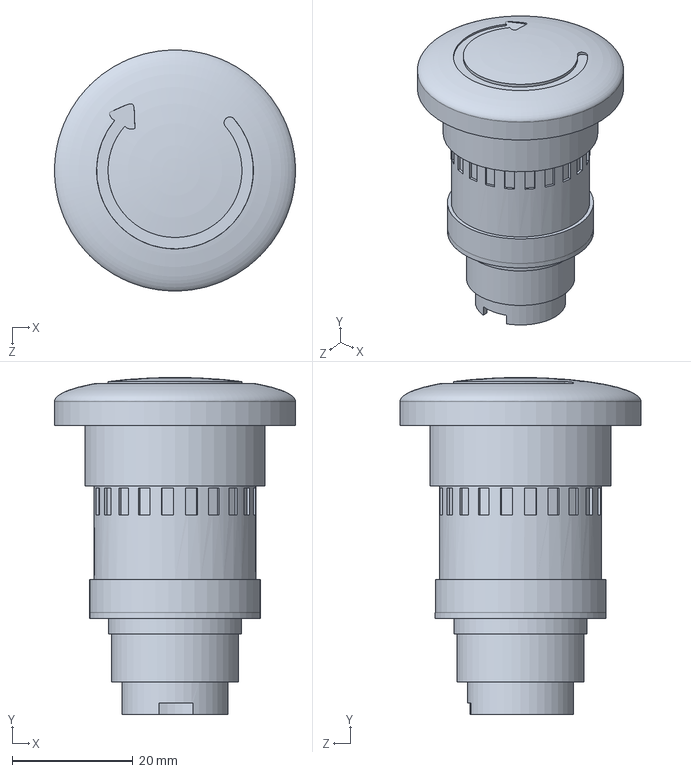
[picture p73: CAD file, 2024-10-19]
solidworks/E-Stop Button [ZB4BS844].SLDPRT
40.0 x 55.9 x 40.0 mm
