ardymarky/TORCH/solidworks/8020-40-4040 X 150.SLDPRT

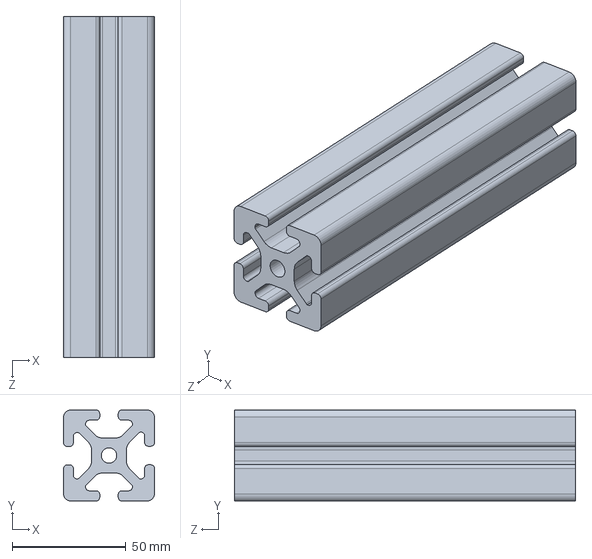
[picture p74: CAD file, 2024-10-18]
solidworks/8020-40-4040 X 150.SLDPRT
40.0 x 40.0 x 150.0 mm
