ardymarky/TORCH/solidworks/Micro Limit Switch.STEP

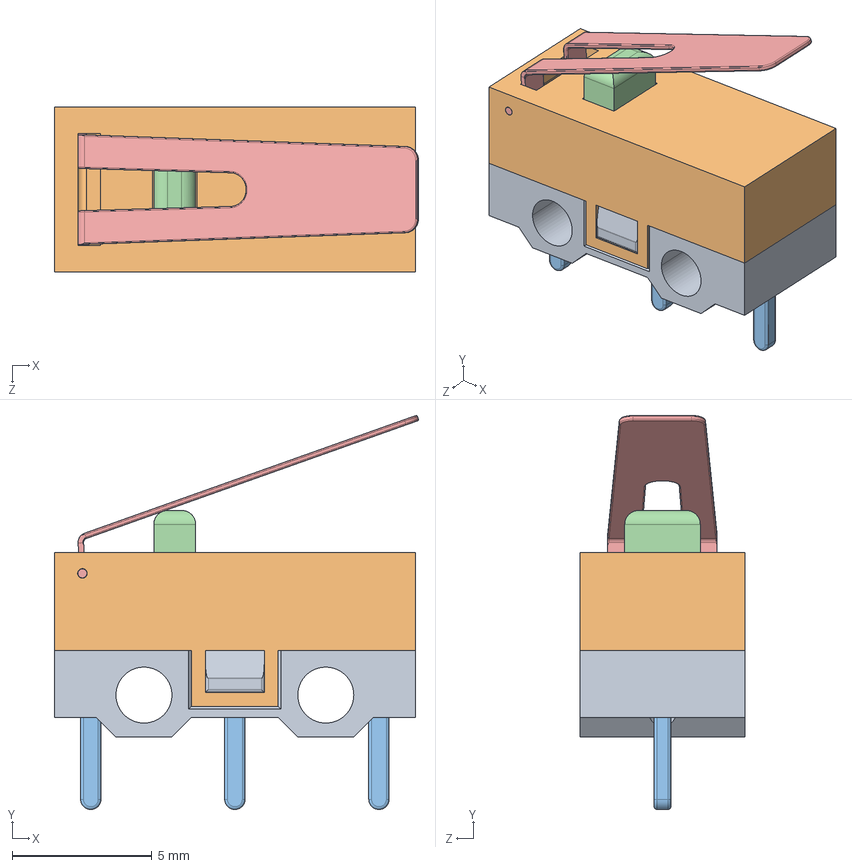
[picture p75: CAD file, 2024-10-16]
solidworks/Micro Limit Switch.STEP
13.0 x 14.1 x 5.90 mm
Bottom
Top
Pins x 3
Button
Lever
