ardymarky/TORCH/solidworks/propguard.SLDPRT

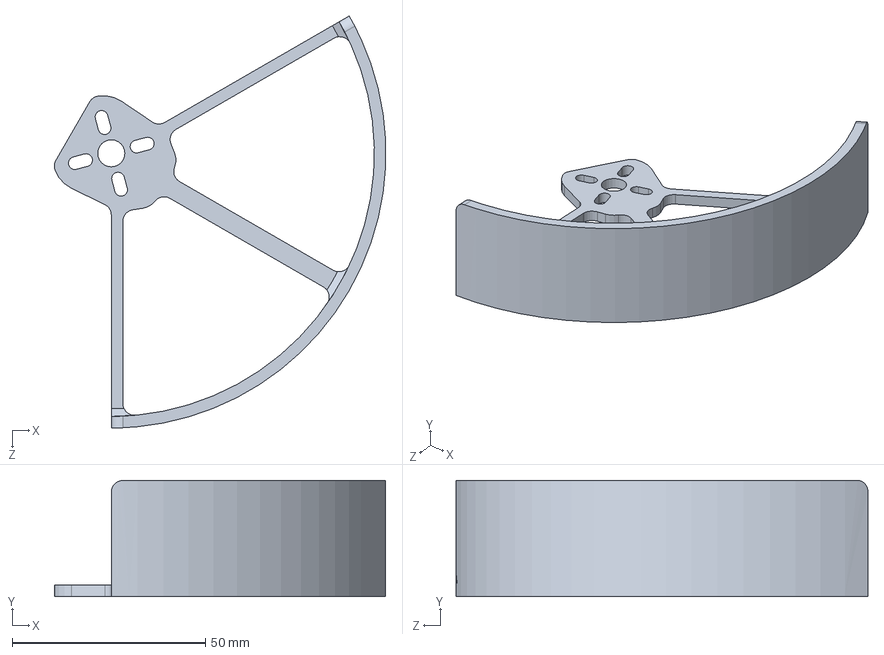
[picture p76: CAD file, 2024-10-11]
solidworks/propguard.SLDPRT
85.6 x 30.0 x 106.5 mm
