ardymarky/TORCH/solidworks/Speedybee F7V3.step

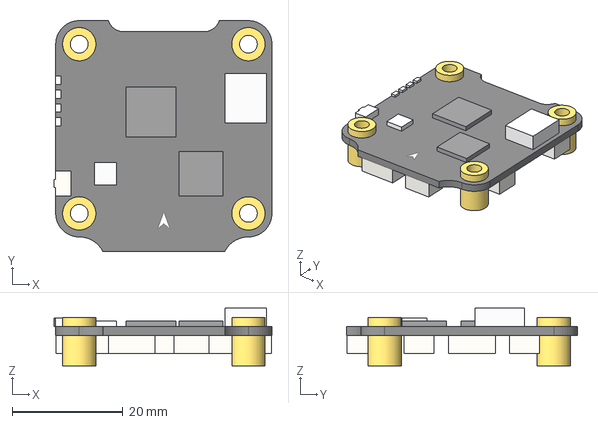
[picture p77: CAD file, 2024-10-11]
solidworks/Speedybee F7V3.step
39.3 x 41.6 x 10.4 mm
