ardymarky/TORCH/solidworks/T Motor F90 2806 1500kV.SLDPRT

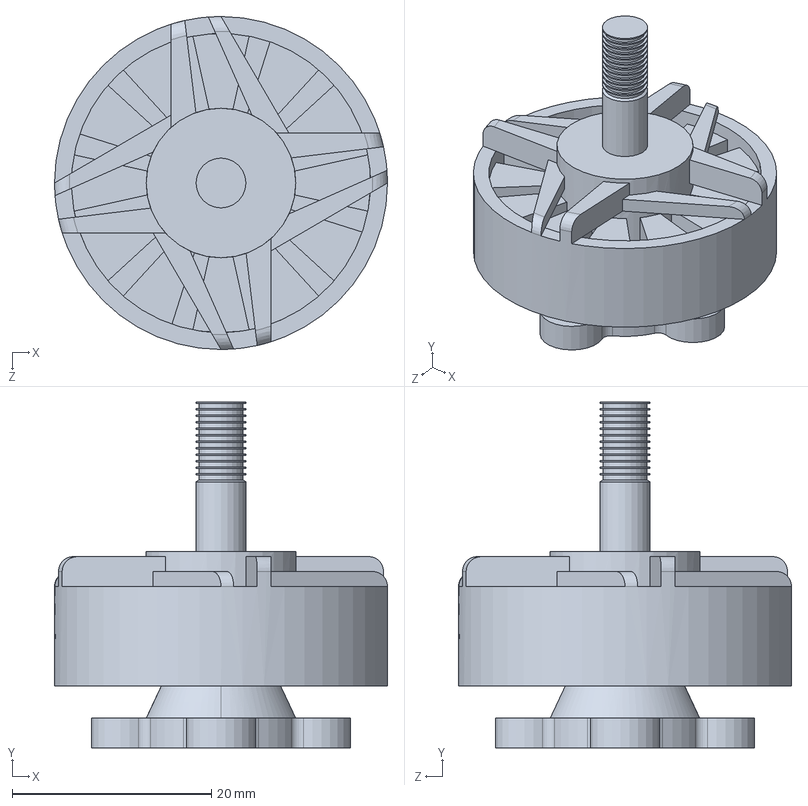
[picture p78: CAD file, 2024-10-11]
solidworks/T Motor F90 2806 1500kV.SLDPRT
33.4 x 34.7 x 33.4 mm
