ardymarky/TORCH/solidworks/8020-40-4040 X 30.SLDPRT

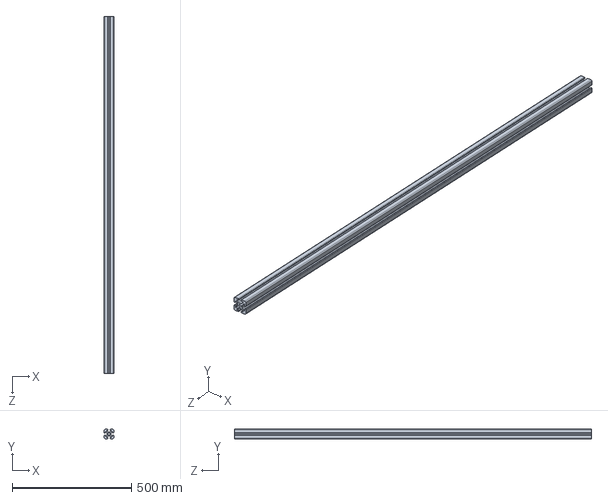
[picture p79: CAD file, 2024-10-11]
solidworks/8020-40-4040 X 30.SLDPRT
40.0 x 40.0 x 1500.0 mm
