ardymarky/TORCH/solidworks/T-Motor F100 2810 KV1350 Rotor.SLDPRT

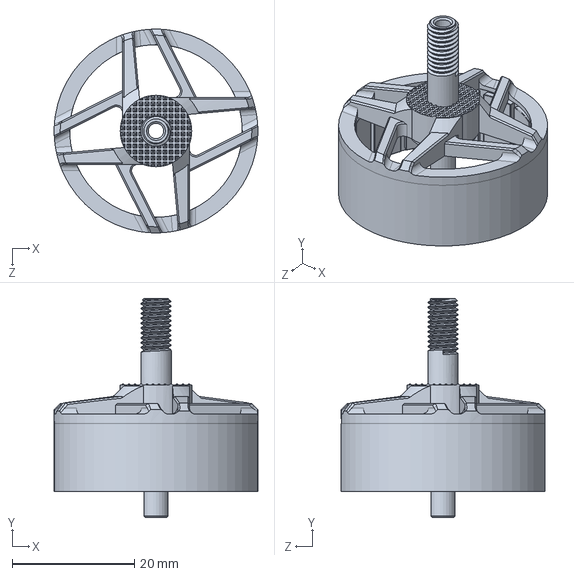
[picture p80: CAD file, 2024-10-11]
solidworks/T-Motor F100 2810 KV1350 Rotor.SLDPRT
33.4 x 35.9 x 33.4 mm
