ardymarky/TORCH/solidworks/sc10uu.SLDPRT

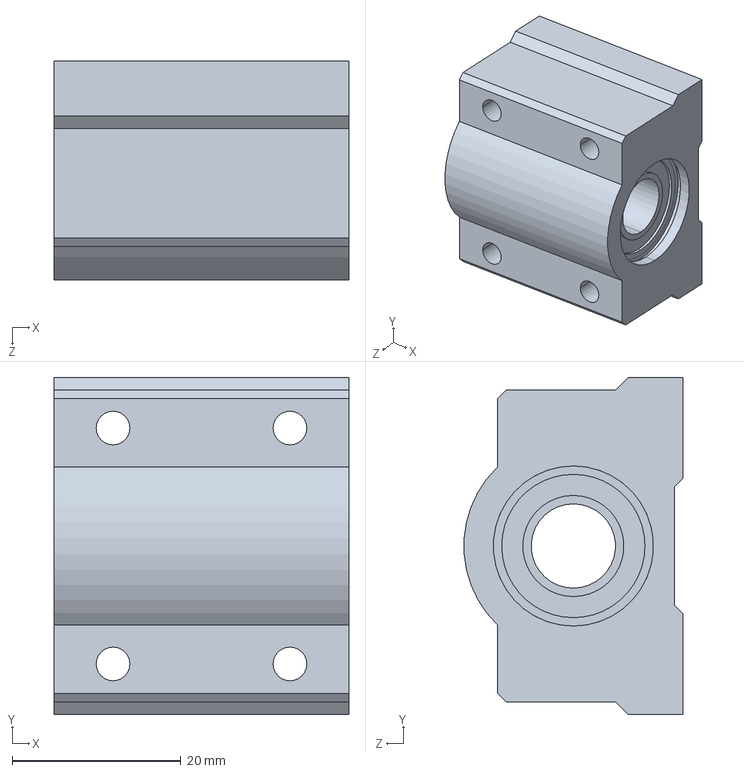
[picture p81: CAD file, 2024-10-11]
solidworks/sc10uu.SLDPRT
35.0 x 40.0 x 26.0 mm
