ardymarky/TORCH/solidworks/8020-40-4040 X 750mm.SLDPRT

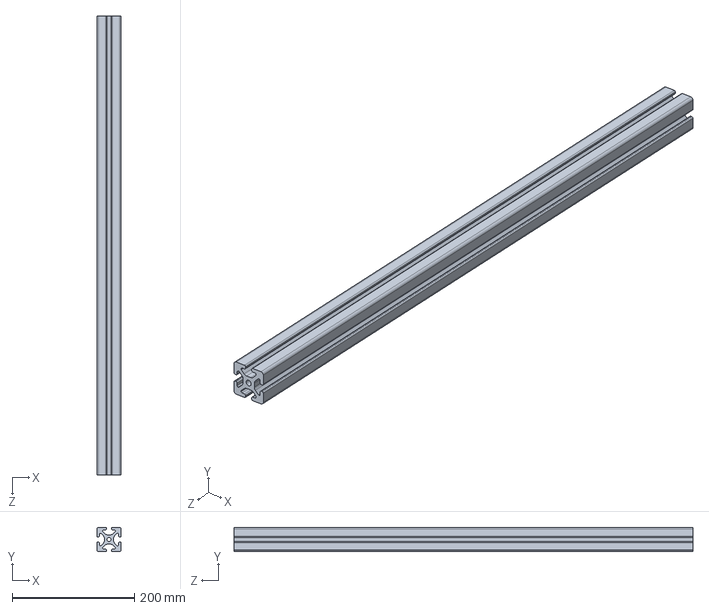
[picture p82: CAD file, 2024-10-11]
solidworks/8020-40-4040 X 750mm.SLDPRT
40.0 x 40.0 x 750.0 mm
