ardymarky/TORCH/solidworks/SPEEDYBEE_BL32_50A_V3.step

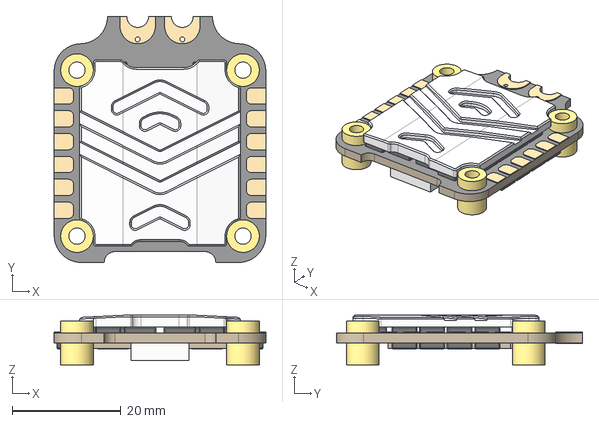
[picture p83: CAD file, 2024-10-11]
solidworks/SPEEDYBEE_BL32_50A_V3.step
38.9 x 45.2 x 9.10 mm
