ardymarky/TORCH/solidworks/L_BEAM_X_MOTION.SLDPRT

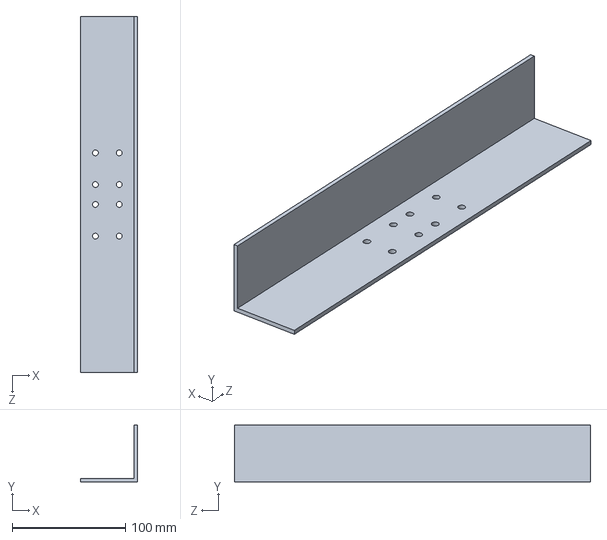
[picture p84: CAD file, 2024-10-11]
solidworks/L_BEAM_X_MOTION.SLDPRT
50.0 x 50.0 x 314.8 mm
