ardymarky/TORCH/solidworks/9506T3_Clamping Shaft Collar.SLDPRT

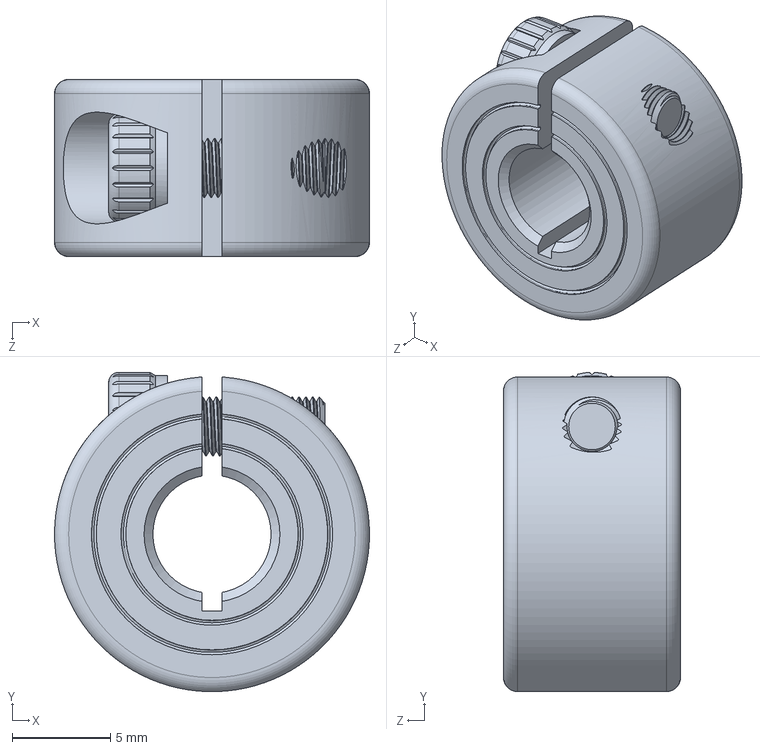
[picture p85: CAD file, 2024-10-11]
solidworks/9506T3_Clamping Shaft Collar.SLDPRT
16.0 x 16.2 x 9.00 mm
