ardymarky/TORCH/solidworks/8004K3_Stainless Steel Mixer Propeller.SLDPRT

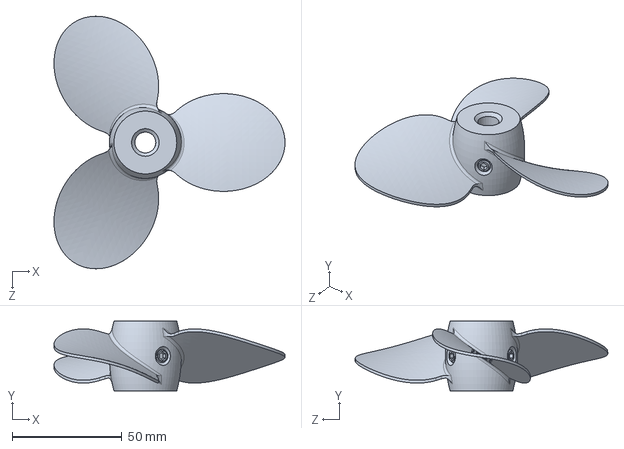
[picture p86: CAD file, 2024-10-11]
solidworks/8004K3_Stainless Steel Mixer Propeller.SLDPRT
105.0 x 31.8 x 114.8 mm
