ardymarky/TORCH/solidworks/SPF455A 4in1 ESC.step

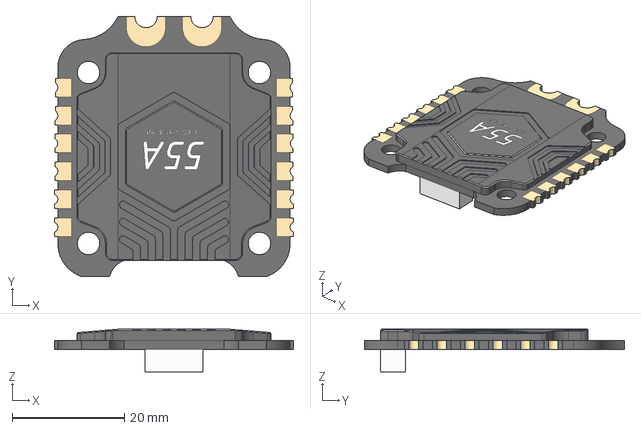
[picture p87: CAD file, 2024-10-11]
solidworks/SPF455A 4in1 ESC.step
42.7 x 46.4 x 7.60 mm
