ardymarky/TORCH/solidworks/Linear Motion Shaft Deflection Test.SLDPRT

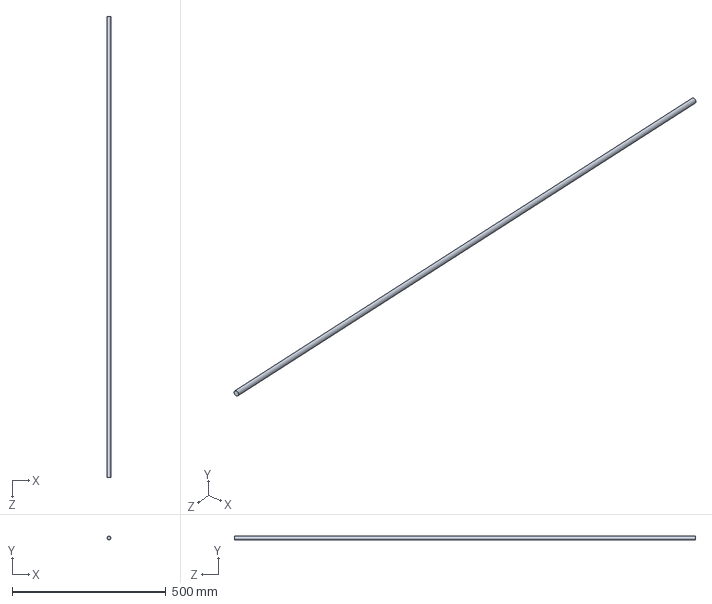
[picture p88: CAD file, 2024-10-11]
solidworks/Linear Motion Shaft Deflection Test.SLDPRT
12.0 x 12.0 x 1500.0 mm
