ardymarky/TORCH/solidworks/8020-40-4040 X 1200mm.SLDPRT

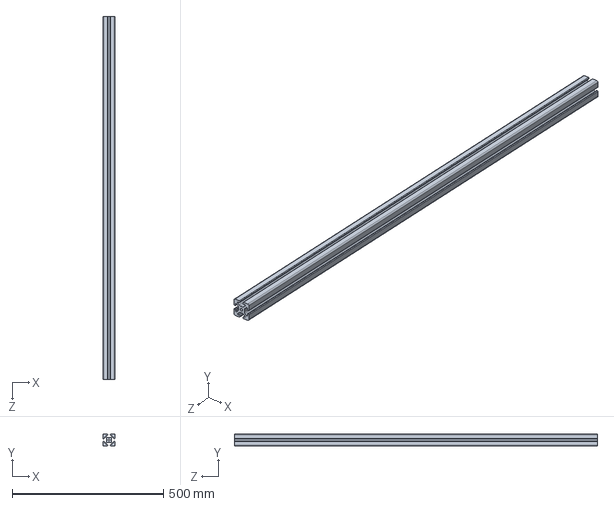
[picture p89: CAD file, 2024-10-11]
solidworks/8020-40-4040 X 1200mm.SLDPRT
40.0 x 40.0 x 1200.0 mm
