ardymarky/TORCH/solidworks/2435K1_Idler Rotary Shaft.SLDPRT

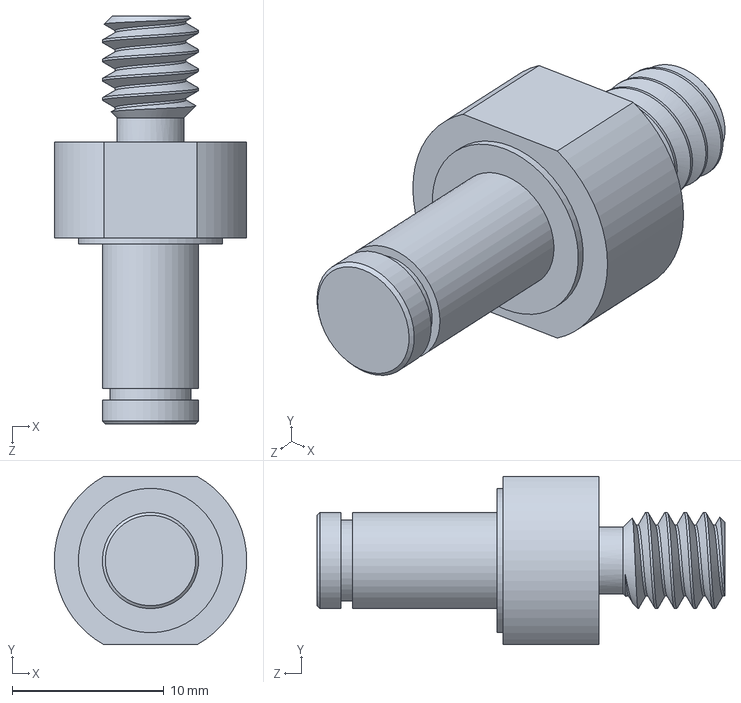
[picture p90: CAD file, 2024-10-11]
solidworks/2435K1_Idler Rotary Shaft.SLDPRT
12.7 x 11.1 x 26.9 mm
