ardymarky/TORCH/solidworks/TOF Range FInder.SLDPRT

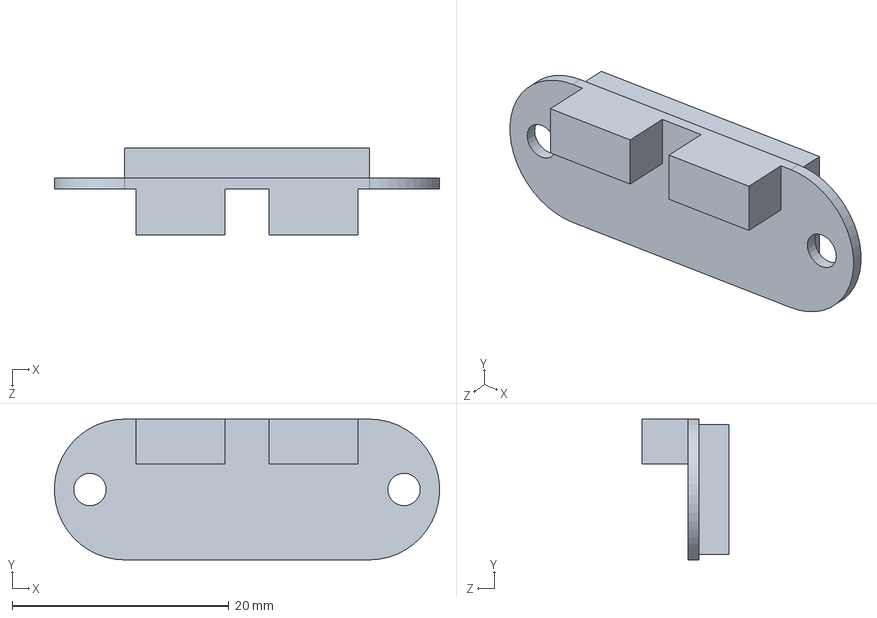
[picture p91: CAD file, 2024-10-11]
solidworks/TOF Range FInder.SLDPRT
35.5 x 13.0 x 8.05 mm
