ardymarky/TORCH/solidworks/8020-40-4040 X 355mm.SLDPRT

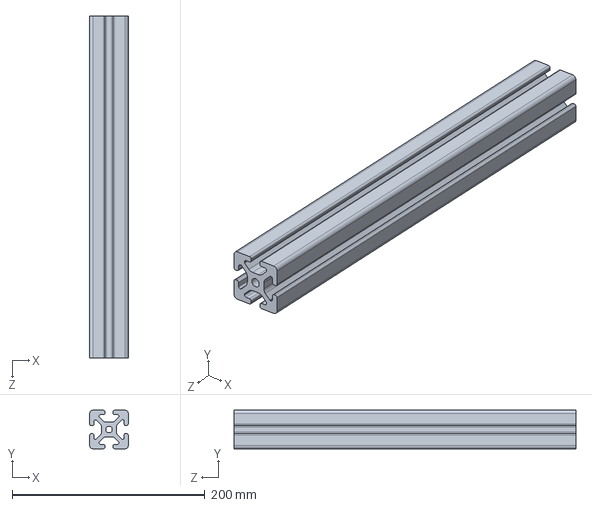
[picture p92: CAD file, 2024-10-11]
solidworks/8020-40-4040 X 355mm.SLDPRT
40.0 x 40.0 x 355.0 mm
