ardymarky/TORCH/solidworks/L_BEAM_X_MOTION_V2.SLDPRT

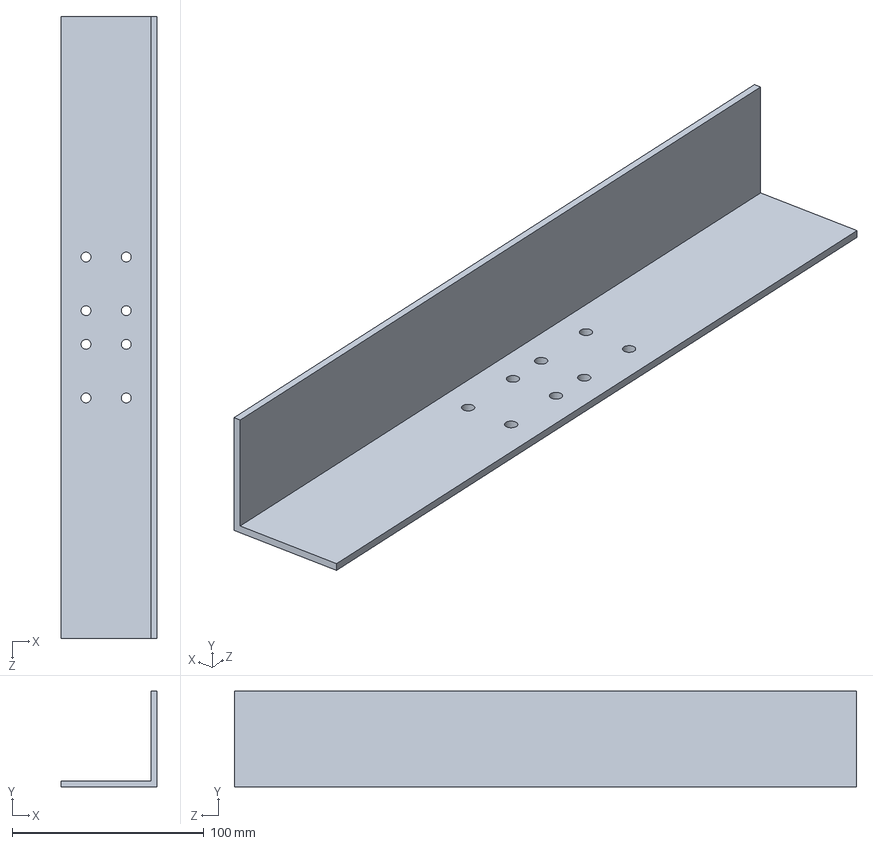
[picture p93: CAD file, 2024-10-11]
solidworks/L_BEAM_X_MOTION_V2.SLDPRT
50.0 x 50.0 x 324.8 mm
