ardymarky/TORCH/solidworks/LinearRail-LWL7B-1500mm.SLDPRT

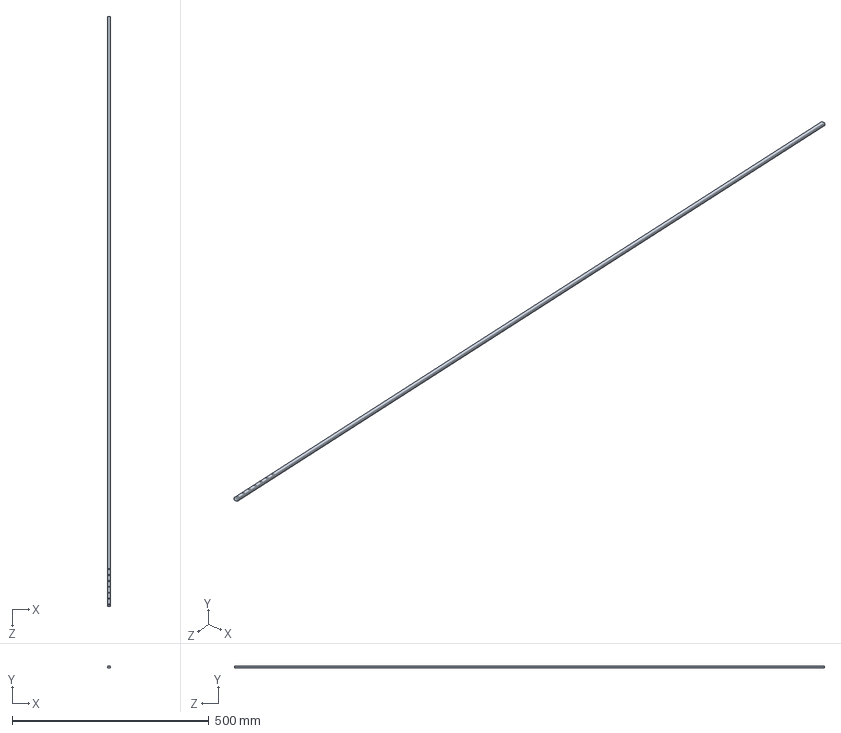
[picture p94: CAD file, 2024-10-11]
solidworks/LinearRail-LWL7B-1500mm.SLDPRT
7.00 x 4.80 x 1500.0 mm
