ardymarky/TORCH/solidworks/innerrail.SLDASM

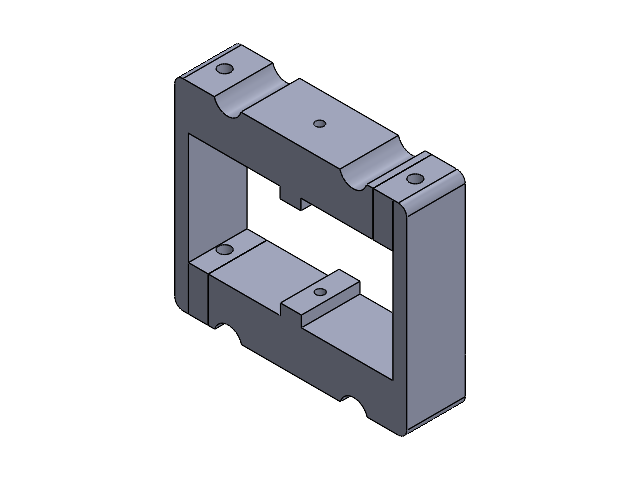
[picture p106: CAD file, 2024-10-23]
solidworks/innerrail.SLDASM
Linear_rail_hold_V4 x 2
