ardymarky/TORCH/solidworks/Linear_rail_hold_V4_3.SLDPRT.SLDASM

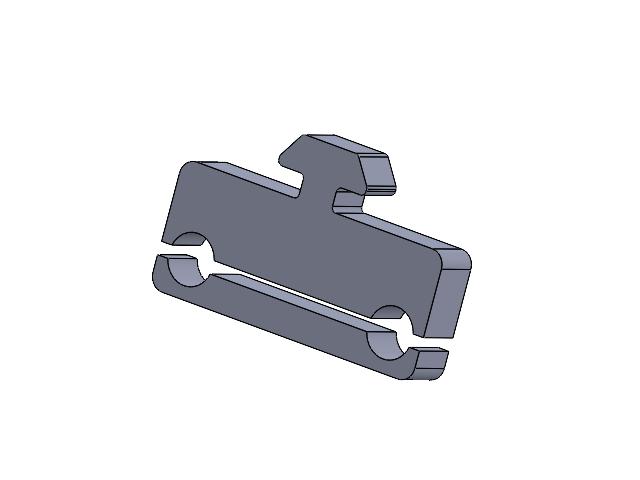
[picture p107: CAD file, 2024-10-23]
solidworks/Linear_rail_hold_V4_3.SLDPRT.SLDASM
Linear_rail_hold_V4_2
Linear_rail_hold_V4
