ardymarky/TORCH/solidworks/E-Stop With Housing.SLDASM

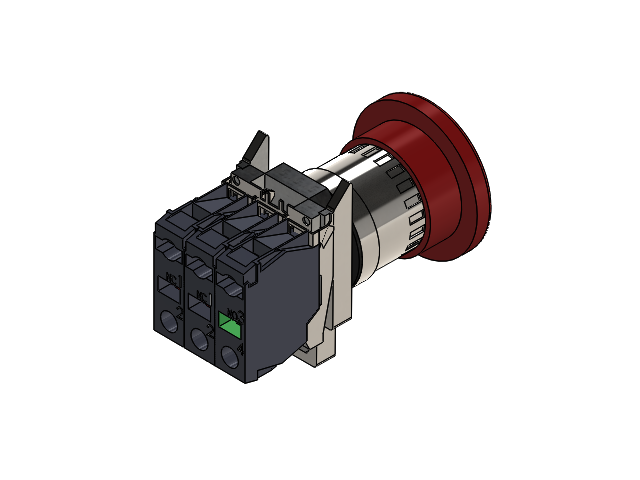
[picture p108: CAD file, 2024-10-19]
solidworks/E-Stop With Housing.SLDASM
NO Contact [ZBE-101]
NC Contact [ZBE-102] x 2
E-Stop Button [ZB4BS844]
Button Housing [ZB4BZ102]
